slu4coder/The-Minimal-64-Home-Computer/Revision 1.2/KiCAD/8-Bit CPU 32k.kicad_sch

## KiCad design Revision 1.2/KiCAD/8-Bit CPU 32k.kicad_sch (2023-07-08)

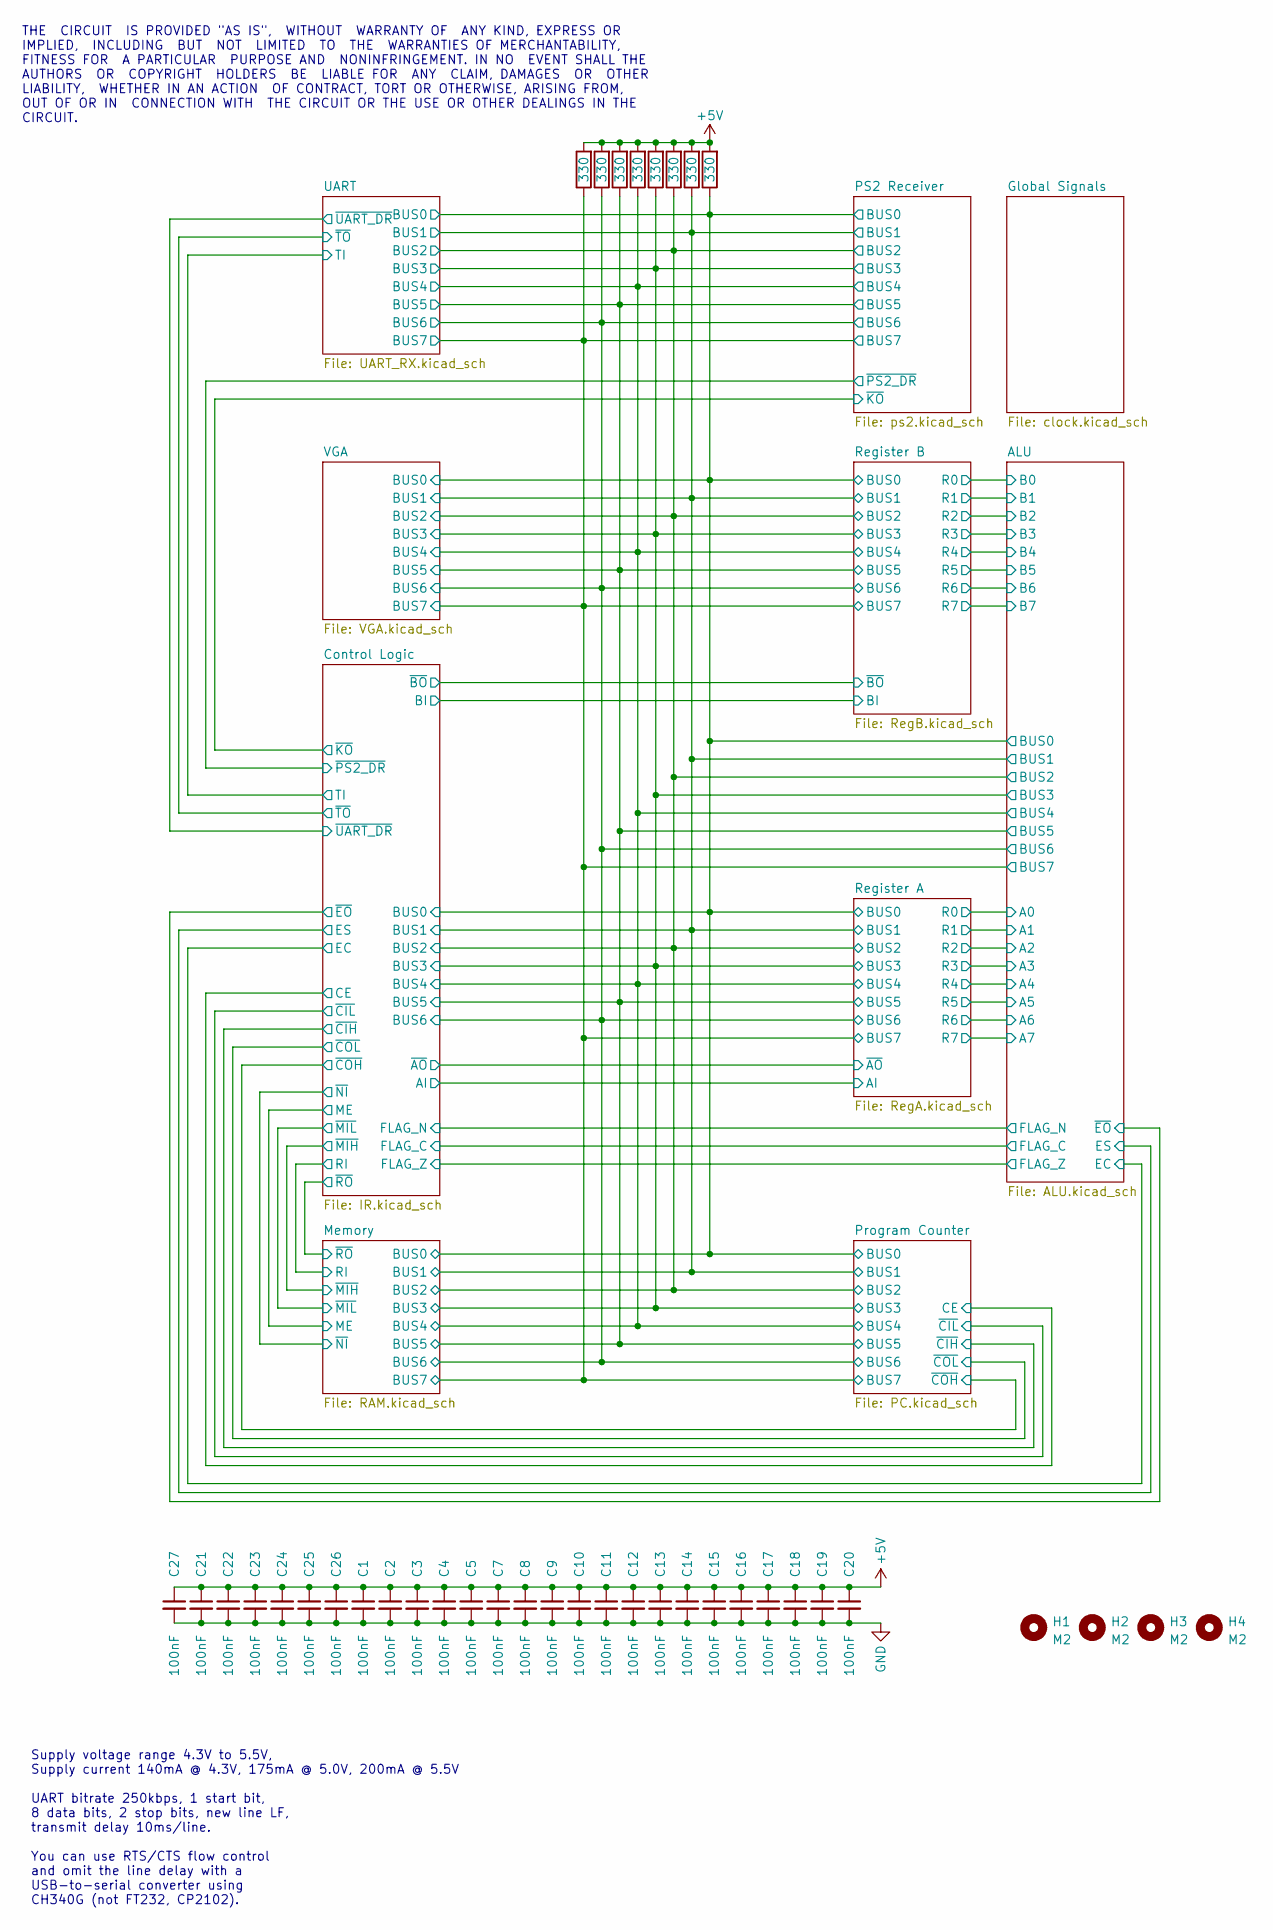
[picture p12: schematic 8-Bit CPU 32k.kicad_sch]

Parts:
C1, C2, C3, C4, C5, C7, C8, C9, C10, C11, C12, C13, C14, C15, C16, C17, C18, C19, C20, C21, C22, C23, C24, C25, C26, C27: 100nF; C_Disc_D3.4mm_W2.1mm_P2.50mm
H1, H2, H3, H4: M2; MountingHole_2.2mm_M2
R25, R26, R27, R28, R29, R30, R31, R32: 330; R_Axial_DIN0207_L6.3mm_D2.5mm_P7.62mm_Horizontal

Connections:
+5V: C1.1, C2.1, C3.1, C4.1, C5.1, C7.1, C8.1, C9.1, C10.1, C11.1, C12.1, C13.1, C14.1, C15.1, C16.1, C17.1, C18.1, C19.1, C20.1, C21.1, C22.1, C23.1, C24.1, C25.1, C26.1, C27.1, R25.2, R26.2, R27.2, R28.2, R29.2, R30.2, R31.2, R32.2
BUS0: R32.1
BUS1: R31.1
BUS2: R30.1
BUS3: R29.1
BUS4: R28.1
BUS5: R27.1
BUS6: R26.1
BUS7: R25.1
GND: C1.2, C2.2, C3.2, C4.2, C5.2, C7.2, C8.2, C9.2, C10.2, C11.2, C12.2, C13.2, C14.2, C15.2, C16.2, C17.2, C18.2, C19.2, C20.2, C21.2, C22.2, C23.2, C24.2, C25.2, C26.2, C27.2

Notes on the sheet:
Supply voltage range 4.3V to 5.5V, Supply current 140mA @ 4.3V, 175mA @ 5.0V, 200mA @ 5.5V UART bitrate 250kbps, 1 start bit, 8 data bits, 2 stop bits, new line LF, transmit delay 10ms/line. You can use RTS/CTS flow control and omit the line delay with a USB-to-serial converter using CH340G (not FT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
THE CIRCUIT IS PROVIDED "AS IS", WITHOUT WARRANTY OF ANY KIND, EXPRESS OR IMPLIED, INCLUDING BUT NOT LIMITED TO THE WARRANTIES OF MERCHANTABILITY, FITNESS FOR A PARTICULAR PURPOSE AND NONINFRINGEMENT. IN NO EVENT SHALL THE AUTHORS OR COPYRIGHT HOLDERS BE LIABLE FOR ANY CLAIM, DAMAGES OR OTHER LIABI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
