slu4coder/The-Minimal-64-Home-Computer/Revision 1.2/KiCAD/ALU.kicad_sch

## KiCad design Revision 1.2/KiCAD/ALU.kicad_sch (2023-07-08)

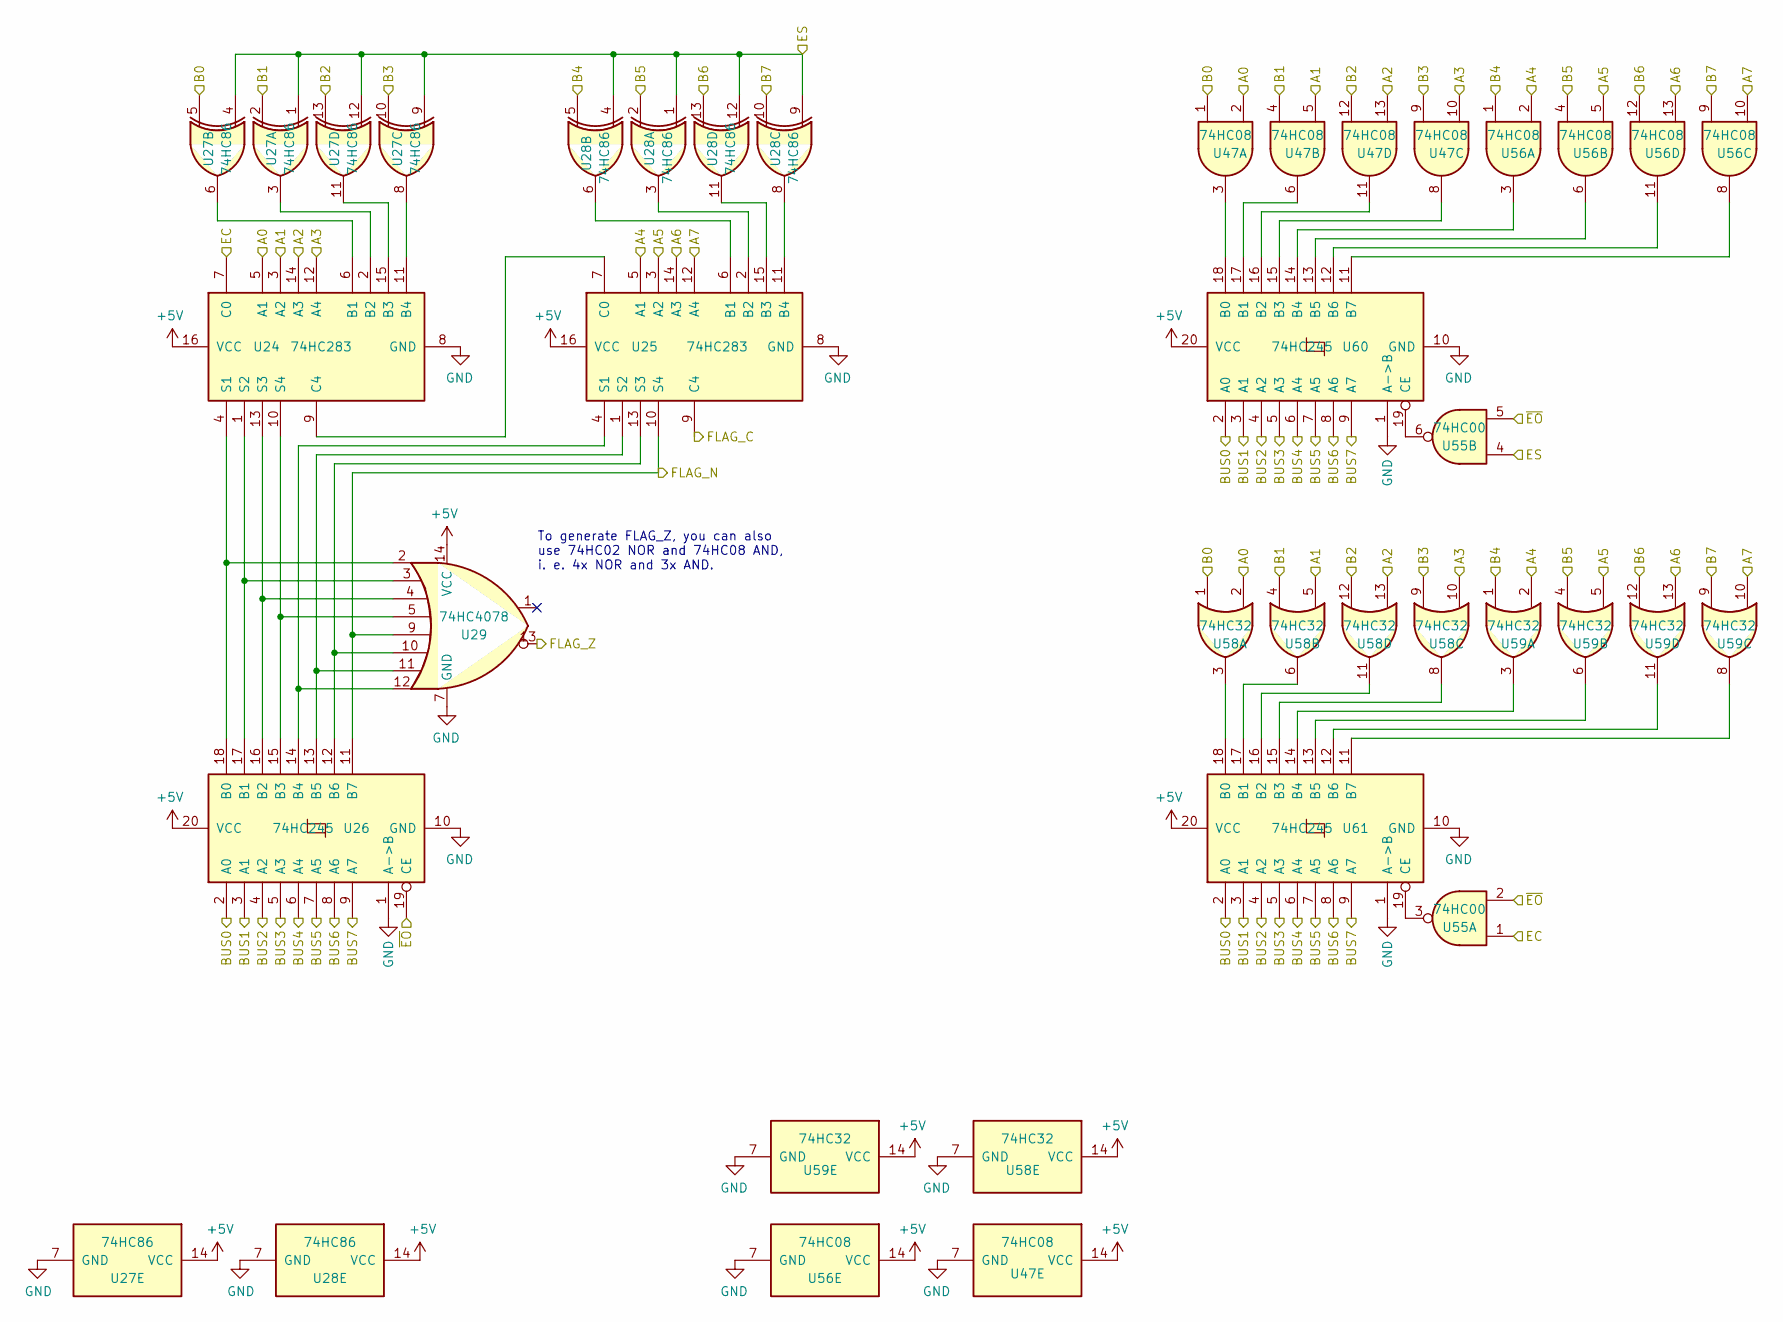
[picture p13: schematic ALU.kicad_sch]

Parts:
U24, U25: 74HC283; DIP-16_W7.62mm
U26, U60, U61: 74HC245; DIP-20_W7.62mm
U27, U28: 74HC86; DIP-14_W7.62mm
U29: 74HC4078; DIP-14_W7.62mm
U47, U56: 74HC08; DIP-14_W7.62mm
U55: 74HC00; DIP-14_W7.62mm
U58, U59: 74HC32; DIP-14_W7.62mm

Connections:
+5V: U24.16 (VCC), U25.16 (VCC), U26.20 (VCC), U27.14 (VCC), U28.14 (VCC), U29.14 (VCC), U47.14 (VCC), U56.14 (VCC), U58.14 (VCC), U59.14 (VCC), U60.20 (VCC), U61.20 (VCC)
A0: U24.5 (A1), U47.2, U58.2
A1: U24.3 (A2), U47.5, U58.5
A2: U24.14 (A3), U47.13, U58.13
A3: U24.12 (A4), U47.10, U58.10
A4: U25.5 (A1), U56.2, U59.2
A5: U25.3 (A2), U56.5, U59.5
A6: U25.14 (A3), U56.13, U59.13
A7: U25.12 (A4), U56.10, U59.10
B0: U27.5, U47.1, U58.1
B1: U27.2, U47.4, U58.4
B2: U27.13, U47.12, U58.12
B3: U27.10, U47.9, U58.9
B4: U28.5, U56.1, U59.1
B5: U28.2, U56.4, U59.4
B6: U28.13, U56.12, U59.12
B7: U28.10, U56.9, U59.9
BUS0: U26.2 (A0), U60.2 (A0), U61.2 (A0)
BUS1: U26.3 (A1), U60.3 (A1), U61.3 (A1)
BUS2: U26.4 (A2), U60.4 (A2), U61.4 (A2)
BUS3: U26.5 (A3), U60.5 (A3), U61.5 (A3)
BUS4: U26.6 (A4), U60.6 (A4), U61.6 (A4)
BUS5: U26.7 (A5), U60.7 (A5), U61.7 (A5)
BUS6: U26.8 (A6), U60.8 (A6), U61.8 (A6)
BUS7: U26.9 (A7), U60.9 (A7), U61.9 (A7)
EC: U24.7 (C0), U55.1
ES: U27.1, U27.4, U27.9, U27.12, U28.1, U28.4, U28.9, U28.12, U55.4
FLAG_C: U25.9 (C4)
FLAG_N: U25.10 (S4), U26.11 (B7), U29.9
FLAG_Z: U29.13
GND: U24.8 (GND), U25.8 (GND), U26.1 (A->B), U26.10 (GND), U27.7 (GND), U28.7 (GND), U29.7 (GND), U47.7 (GND), U56.7 (GND), U58.7 (GND), U59.7 (GND), U60.1 (A->B), U60.10 (GND), U61.1 (A->B), U61.10 (GND)
unnamed: U24.1 (S2), U26.17 (B1), U29.3
unnamed: U24.2 (B2), U27.3
unnamed: U24.4 (S1), U26.18 (B0), U29.2
unnamed: U24.6 (B1), U27.6
unnamed: U24.9 (C4), U25.7 (C0)
unnamed: U24.10 (S4), U26.15 (B3), U29.5
unnamed: U24.11 (B4), U27.8
unnamed: U24.13 (S3), U26.16 (B2), U29.4
unnamed: U24.15 (B3), U27.11
unnamed: U25.1 (S2), U26.13 (B5), U29.11
unnamed: U25.2 (B2), U28.3
unnamed: U25.4 (S1), U26.14 (B4), U29.12
unnamed: U25.6 (B1), U28.6
unnamed: U25.11 (B4), U28.8
unnamed: U25.13 (S3), U26.12 (B6), U29.10
unnamed: U25.15 (B3), U28.11
unnamed: U47.3, U60.18 (B0)
unnamed: U47.6, U60.17 (B1)
unnamed: U47.8, U60.15 (B3)
unnamed: U47.11, U60.16 (B2)
unnamed: U55.3, U61.19 (CE)
unnamed: U55.6, U60.19 (CE)
unnamed: U56.3, U60.14 (B4)
unnamed: U56.6, U60.13 (B5)
unnamed: U56.8, U60.11 (B7)
unnamed: U56.11, U60.12 (B6)
unnamed: U58.3, U61.18 (B0)
unnamed: U58.6, U61.17 (B1)
unnamed: U58.8, U61.15 (B3)
unnamed: U58.11, U61.16 (B2)
unnamed: U59.3, U61.14 (B4)
unnamed: U59.6, U61.13 (B5)
unnamed: U59.8, U61.11 (B7)
unnamed: U59.11, U61.12 (B6)
~EO: U26.19 (CE), U55.2, U55.5

Notes on the sheet:
To generate FLAG_Z, you can also use 74HC02 NOR and 74HC08 AND, i. e. 4x NOR and 3x AND.
