slu4coder/The-Minimal-64-Home-Computer/Revision 1.2/KiCAD/IR.kicad_sch

## KiCad design Revision 1.2/KiCAD/IR.kicad_sch (2023-07-08)

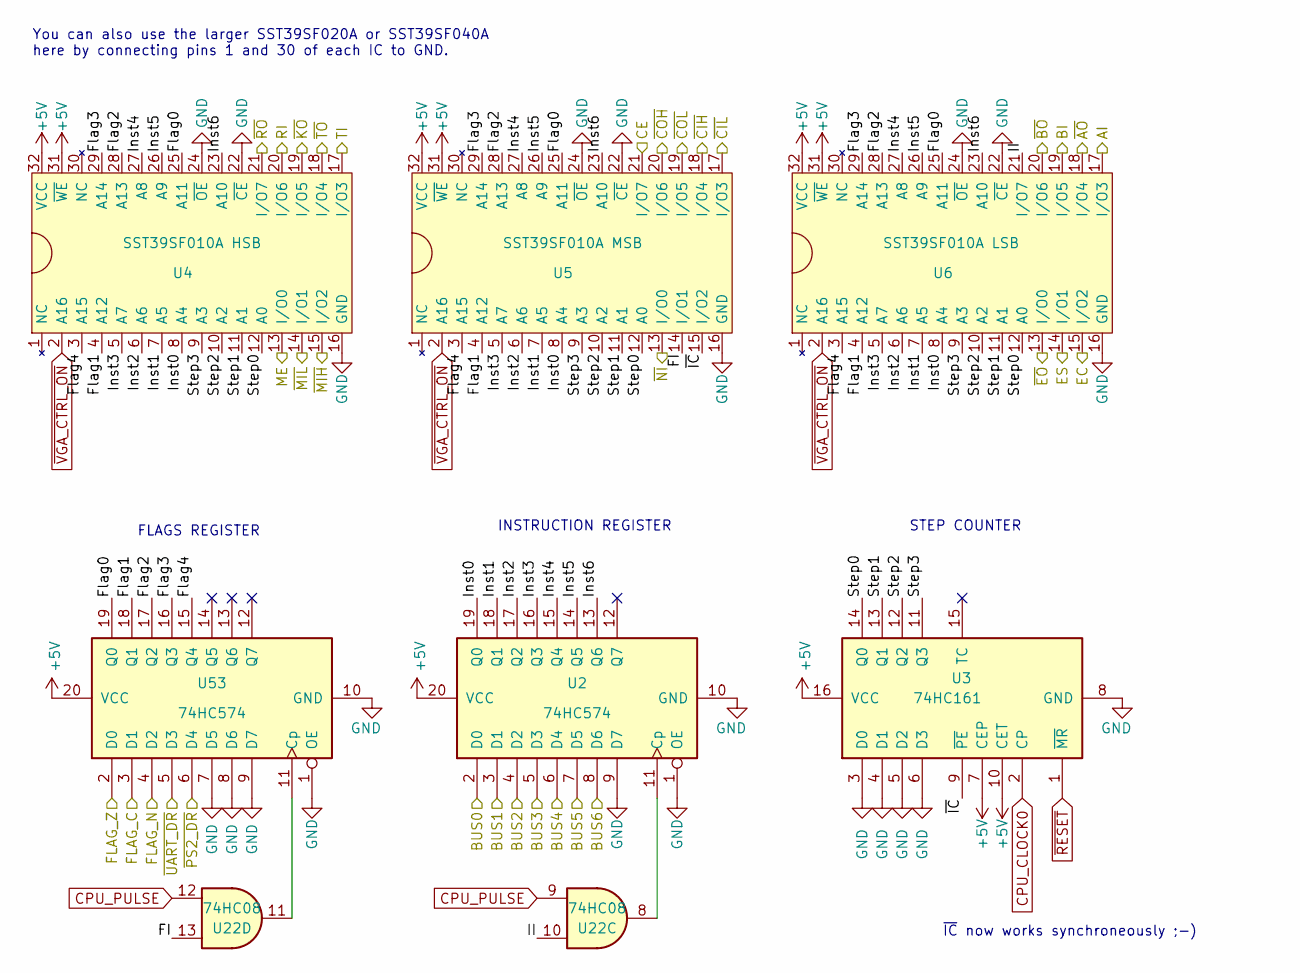
[picture p14: schematic IR.kicad_sch]

Parts:
U2, U53: 74HC574; DIP-20_W7.62mm
U3: 74HC161; DIP-16_W7.62mm
U4: SST39SF010A HSB; DIP-32_W15.24mm_Socket
U5: SST39SF010A MSB; DIP-32_W15.24mm_Socket
U6: SST39SF010A LSB; DIP-32_W15.24mm_Socket
U22: 74HC08; DIP-14_W7.62mm

Connections:
+5V: U2.20 (VCC), U3.7 (CEP), U3.10 (CET), U3.16 (VCC), U4.31 (~WE), U4.32 (VCC), U5.31 (~WE), U5.32 (VCC), U6.31 (~WE), U6.32 (VCC), U53.20 (VCC)
AI: U6.17 (I/O3)
BI: U6.19 (I/O5)
BUS0: U2.2 (D0)
BUS1: U2.3 (D1)
BUS2: U2.4 (D2)
BUS3: U2.5 (D3)
BUS4: U2.6 (D4)
BUS5: U2.7 (D5)
BUS6: U2.8 (D6)
CE: U5.21 (I/O7)
CPU_CLOCK0: U3.2 (CP)
CPU_PULSE: U22.9, U22.12
EC: U6.15 (I/O2)
ES: U6.14 (I/O1)
FI: U5.14 (I/O1), U22.13
FLAG_C: U53.3 (D1)
FLAG_N: U53.4 (D2)
FLAG_Z: U53.2 (D0)
Flag0: U4.25 (A11), U5.25 (A11), U6.25 (A11), U53.19 (Q0)
Flag1: U4.4 (A12), U5.4 (A12), U6.4 (A12), U53.18 (Q1)
Flag2: U4.28 (A13), U5.28 (A13), U6.28 (A13), U53.17 (Q2)
Flag3: U4.29 (A14), U5.29 (A14), U6.29 (A14), U53.16 (Q3)
Flag4: U4.3 (A15), U5.3 (A15), U6.3 (A15), U53.15 (Q4)
GND: U2.1 (OE), U2.9 (D7), U2.10 (GND), U3.3 (D0), U3.4 (D1), U3.5 (D2), U3.6 (D3), U3.8 (GND), U4.16 (GND), U4.22 (~CE), U4.24 (~OE), U5.16 (GND), U5.22 (~CE), U5.24 (~OE), U6.16 (GND), U6.22 (~CE), U6.24 (~OE), U53.1 (OE), U53.7 (D5), U53.8 (D6), U53.9 (D7), U53.10 (GND)
II: U6.21 (I/O7), U22.10
Inst0: U2.19 (Q0), U4.8 (A4), U5.8 (A4), U6.8 (A4)
Inst1: U2.18 (Q1), U4.7 (A5), U5.7 (A5), U6.7 (A5)
Inst2: U2.17 (Q2), U4.6 (A6), U5.6 (A6), U6.6 (A6)
Inst3: U2.16 (Q3), U4.5 (A7), U5.5 (A7), U6.5 (A7)
Inst4: U2.15 (Q4), U4.27 (A8), U5.27 (A8), U6.27 (A8)
Inst5: U2.14 (Q5), U4.26 (A9), U5.26 (A9), U6.26 (A9)
Inst6: U2.13 (Q6), U4.23 (A10), U5.23 (A10), U6.23 (A10)
ME: U4.13 (I/O0)
unnamed: U2.11 (Cp), U22.8
unnamed: U22.11, U53.11 (Cp)
RI: U4.20 (I/O6)
Step0: U3.14 (Q0), U4.12 (A0), U5.12 (A0), U6.12 (A0)
Step1: U3.13 (Q1), U4.11 (A1), U5.11 (A1), U6.11 (A1)
Step2: U3.12 (Q2), U4.10 (A2), U5.10 (A2), U6.10 (A2)
Step3: U3.11 (Q3), U4.9 (A3), U5.9 (A3), U6.9 (A3)
TI: U4.17 (I/O3)
~AO: U6.18 (I/O4)
~BO: U6.20 (I/O6)
~CIH: U5.18 (I/O4)
~CIL: U5.17 (I/O3)
~COH: U5.20 (I/O6)
~COL: U5.19 (I/O5)
~EO: U6.13 (I/O0)
~IC: U3.9 (~PE), U5.15 (I/O2)
~KO: U4.19 (I/O5)
~MIH: U4.15 (I/O2)
~MIL: U4.14 (I/O1)
~NI: U5.13 (I/O0)
~PS2_DR: U53.6 (D4)
~RESET: U3.1 (~MR)
~RO: U4.21 (I/O7)
~TO: U4.18 (I/O4)
~UART_DR: U53.5 (D3)
~VGA_CTRL_ON: U4.2 (A16), U5.2 (A16), U6.2 (A16)

Notes on the sheet:
FLAGS REGISTER
~{IC} now works synchroneously ;-)
INSTRUCTION REGISTER
You can also use the larger SST39SF020A or SST39SF040A here by connecting pins 1 and 30 of each IC to GND.
STEP COUNTER
