slu4coder/The-Minimal-64-Home-Computer/Revision 1.2/KiCAD/PC.kicad_sch

## KiCad design Revision 1.2/KiCAD/PC.kicad_sch (2023-07-08)

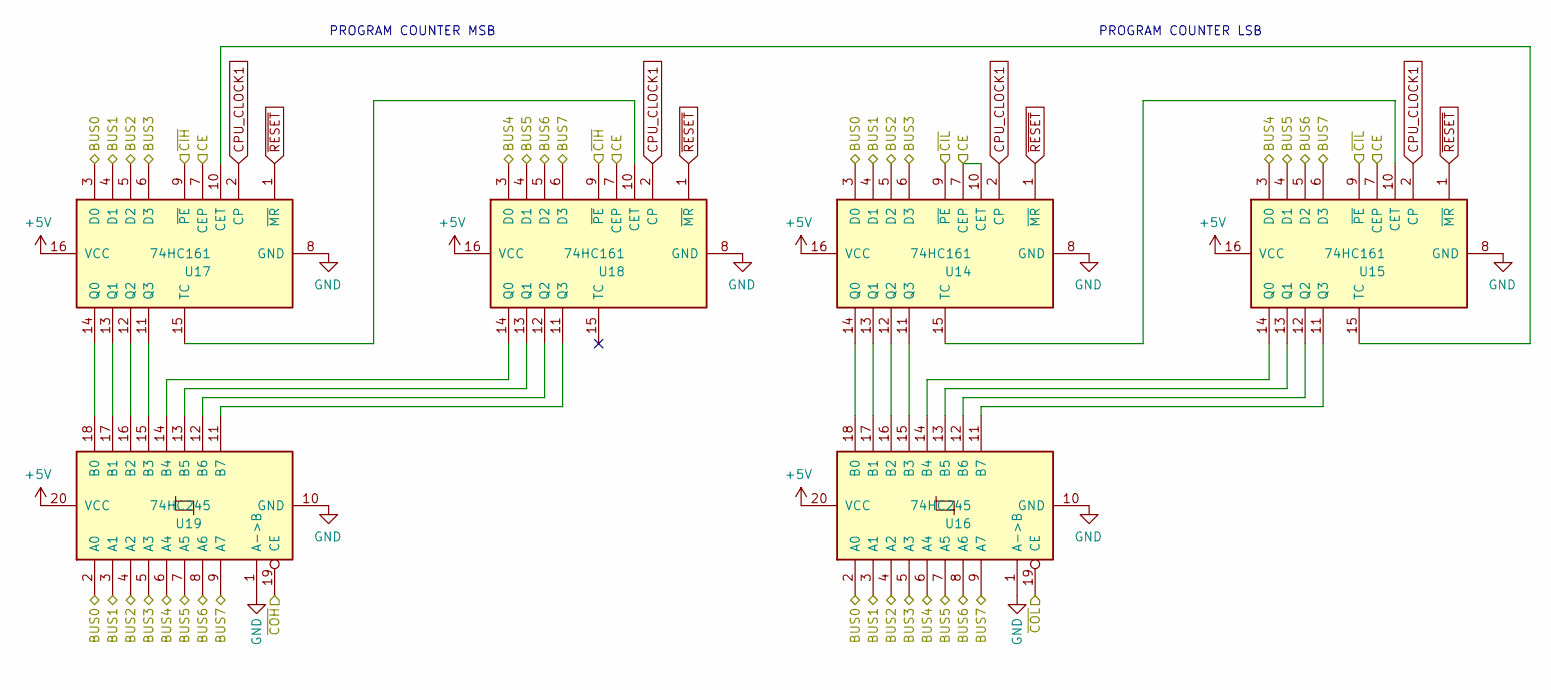
[picture p15: schematic PC.kicad_sch]

Parts:
U14, U15, U17, U18: 74HC161; DIP-16_W7.62mm
U16, U19: 74HC245; DIP-20_W7.62mm

Connections:
+5V: U14.16 (VCC), U15.16 (VCC), U16.20 (VCC), U17.16 (VCC), U18.16 (VCC), U19.20 (VCC)
BUS0: U14.3 (D0), U16.2 (A0), U17.3 (D0), U19.2 (A0)
BUS1: U14.4 (D1), U16.3 (A1), U17.4 (D1), U19.3 (A1)
BUS2: U14.5 (D2), U16.4 (A2), U17.5 (D2), U19.4 (A2)
BUS3: U14.6 (D3), U16.5 (A3), U17.6 (D3), U19.5 (A3)
BUS4: U15.3 (D0), U16.6 (A4), U18.3 (D0), U19.6 (A4)
BUS5: U15.4 (D1), U16.7 (A5), U18.4 (D1), U19.7 (A5)
BUS6: U15.5 (D2), U16.8 (A6), U18.5 (D2), U19.8 (A6)
BUS7: U15.6 (D3), U16.9 (A7), U18.6 (D3), U19.9 (A7)
CE: U14.7 (CEP), U14.10 (CET), U15.7 (CEP), U17.7 (CEP), U18.7 (CEP)
CPU_CLOCK1: U14.2 (CP), U15.2 (CP), U17.2 (CP), U18.2 (CP)
GND: U14.8 (GND), U15.8 (GND), U16.1 (A->B), U16.10 (GND), U17.8 (GND), U18.8 (GND), U19.1 (A->B), U19.10 (GND)
unnamed: U14.11 (Q3), U16.15 (B3)
unnamed: U14.12 (Q2), U16.16 (B2)
unnamed: U14.13 (Q1), U16.17 (B1)
unnamed: U14.14 (Q0), U16.18 (B0)
unnamed: U14.15 (TC), U15.10 (CET)
unnamed: U15.11 (Q3), U16.11 (B7)
unnamed: U15.12 (Q2), U16.12 (B6)
unnamed: U15.13 (Q1), U16.13 (B5)
unnamed: U15.14 (Q0), U16.14 (B4)
unnamed: U15.15 (TC), U17.10 (CET)
unnamed: U17.11 (Q3), U19.15 (B3)
unnamed: U17.12 (Q2), U19.16 (B2)
unnamed: U17.13 (Q1), U19.17 (B1)
unnamed: U17.14 (Q0), U19.18 (B0)
unnamed: U17.15 (TC), U18.10 (CET)
unnamed: U18.11 (Q3), U19.11 (B7)
unnamed: U18.12 (Q2), U19.12 (B6)
unnamed: U18.13 (Q1), U19.13 (B5)
unnamed: U18.14 (Q0), U19.14 (B4)
~CIH: U17.9 (~PE), U18.9 (~PE)
~CIL: U14.9 (~PE), U15.9 (~PE)
~COH: U19.19 (CE)
~COL: U16.19 (CE)
~RESET: U14.1 (~MR), U15.1 (~MR), U17.1 (~MR), U18.1 (~MR)

Notes on the sheet:
PROGRAM COUNTER MSB
PROGRAM COUNTER LSB
