slu4coder/The-Minimal-64-Home-Computer/Revision 1.2/KiCAD/RAM.kicad_sch

## KiCad design Revision 1.2/KiCAD/RAM.kicad_sch (2023-07-08)

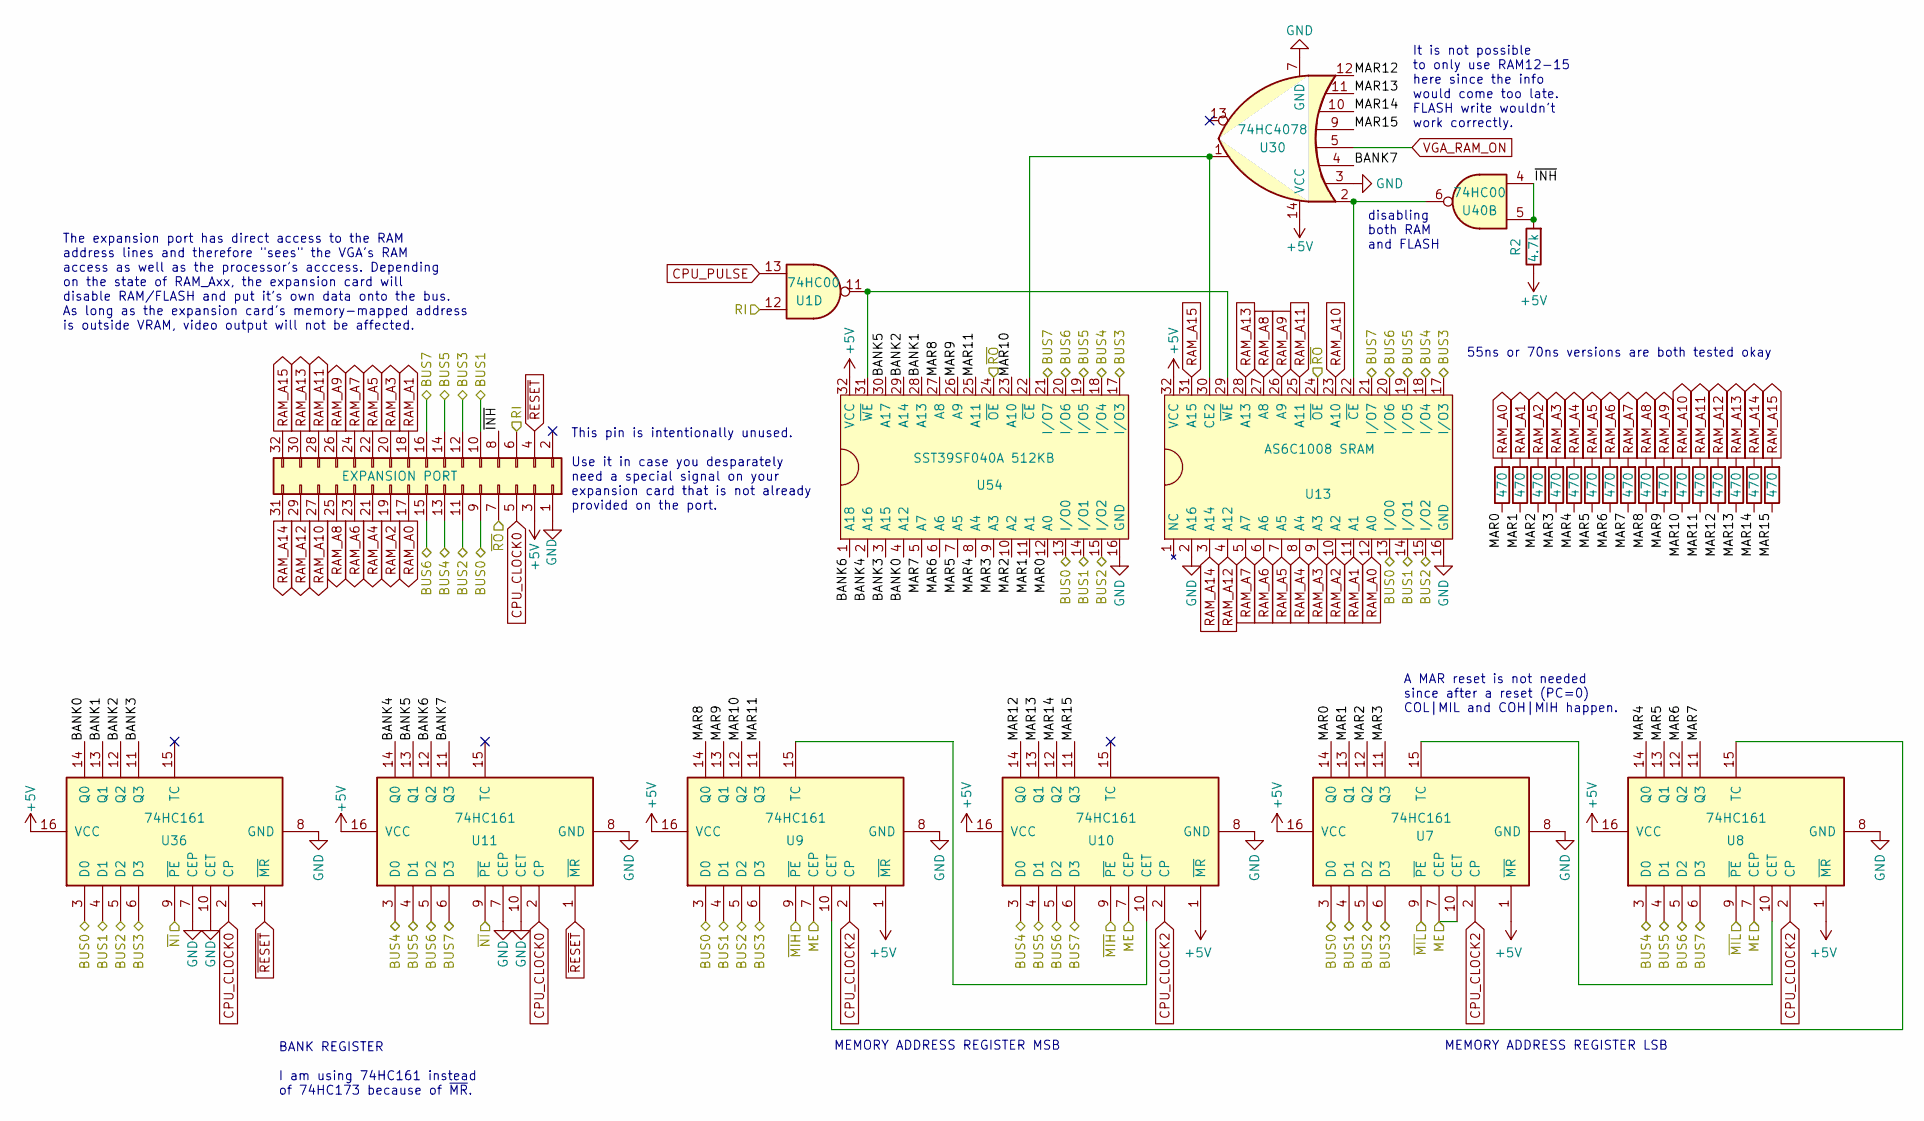
[picture p16: schematic RAM.kicad_sch]

Parts:
J3: EXPANSION PORT; PinSocket_2x16_P2.54mm_Vertical
R2: 4.7k; R_Axial_DIN0207_L6.3mm_D2.5mm_P7.62mm_Horizontal
R5, R6, R7, R8, R9, R10, R11, R12, R13, R14, R15, R16, R17, R18, R19, R20: 470; R_Axial_DIN0207_L6.3mm_D2.5mm_P7.62mm_Horizontal
U1, U40: 74HC00; DIP-14_W7.62mm
U7, U8, U9, U10, U11, U36: 74HC161; DIP-16_W7.62mm
U13: AS6C1008 SRAM; DIP-32_W15.24mm
U30: 74HC4078; DIP-14_W7.62mm
U54: SST39SF040A 512KB; DIP-32_W15.24mm_Socket

Connections:
+5V: J3.3, R2.1, U7.1 (~MR), U7.16 (VCC), U8.1 (~MR), U8.16 (VCC), U9.1 (~MR), U9.16 (VCC), U10.1 (~MR), U10.16 (VCC), U11.16 (VCC), U13.32 (VCC), U30.14 (VCC), U36.16 (VCC), U54.32 (VCC)
BANK0: U36.14 (Q0), U54.4 (A12)
BANK1: U36.13 (Q1), U54.28 (A13)
BANK2: U36.12 (Q2), U54.29 (A14)
BANK3: U36.11 (Q3), U54.3 (A15)
BANK4: U11.14 (Q0), U54.2 (A16)
BANK5: U11.13 (Q1), U54.30 (A17)
BANK6: U11.12 (Q2), U54.1 (A18)
BANK7: U11.11 (Q3), U30.4
BUS0: J3.9, U7.3 (D0), U9.3 (D0), U13.13 (I/O0), U36.3 (D0), U54.13 (I/O0)
BUS1: J3.10, U7.4 (D1), U9.4 (D1), U13.14 (I/O1), U36.4 (D1), U54.14 (I/O1)
BUS2: J3.11, U7.5 (D2), U9.5 (D2), U13.15 (I/O2), U36.5 (D2), U54.15 (I/O2)
BUS3: J3.12, U7.6 (D3), U9.6 (D3), U13.17 (I/O3), U36.6 (D3), U54.17 (I/O3)
BUS4: J3.13, U8.3 (D0), U10.3 (D0), U11.3 (D0), U13.18 (I/O4), U54.18 (I/O4)
BUS5: J3.14, U8.4 (D1), U10.4 (D1), U11.4 (D1), U13.19 (I/O5), U54.19 (I/O5)
BUS6: J3.15, U8.5 (D2), U10.5 (D2), U11.5 (D2), U13.20 (I/O6), U54.20 (I/O6)
BUS7: J3.16, U8.6 (D3), U10.6 (D3), U11.6 (D3), U13.21 (I/O7), U54.21 (I/O7)
CPU_CLOCK0: J3.5, U11.2 (CP), U36.2 (CP)
CPU_CLOCK2: U7.2 (CP), U8.2 (CP), U9.2 (CP), U10.2 (CP)
CPU_PULSE: U1.13
GND: J3.1, U7.8 (GND), U8.8 (GND), U9.8 (GND), U10.8 (GND), U11.7 (CEP), U11.8 (GND), U11.10 (CET), U13.2 (A16), U13.16 (GND), U30.3, U30.7 (GND), U36.7 (CEP), U36.8 (GND), U36.10 (CET), U54.16 (GND)
MAR0: R17.1, U7.14 (Q0), U54.12 (A0)
MAR1: R18.1, U7.13 (Q1), U54.11 (A1)
MAR2: R19.1, U7.12 (Q2), U54.10 (A2)
MAR3: R20.1, U7.11 (Q3), U54.9 (A3)
MAR4: R13.1, U8.14 (Q0), U54.8 (A4)
MAR5: R14.1, U8.13 (Q1), U54.7 (A5)
MAR6: R15.1, U8.12 (Q2), U54.6 (A6)
MAR7: R16.1, U8.11 (Q3), U54.5 (A7)
MAR8: R5.1, U9.14 (Q0), U54.27 (A8)
MAR9: R6.1, U9.13 (Q1), U54.26 (A9)
MAR10: R7.1, U9.12 (Q2), U54.23 (A10)
MAR11: R8.1, U9.11 (Q3), U54.25 (A11)
MAR12: R9.1, U10.14 (Q0), U30.12
MAR13: R10.1, U10.13 (Q1), U30.11
MAR14: R11.1, U10.12 (Q2), U30.10
MAR15: R12.1, U10.11 (Q3), U30.9
ME: U7.7 (CEP), U7.10 (CET), U8.7 (CEP), U9.7 (CEP), U10.7 (CEP)
unnamed: U1.11, U13.29 (~WE), U54.31 (~WE)
unnamed: U7.15 (TC), U8.10 (CET)
unnamed: U8.15 (TC), U9.10 (CET)
unnamed: U9.15 (TC), U10.10 (CET)
unnamed: U13.22 (~CE), U30.2, U40.6
unnamed: U13.30 (CE2), U30.1, U54.22 (~CE)
RAM_A0: J3.17, R17.2, U13.12 (A0)
RAM_A1: J3.18, R18.2, U13.11 (A1)
RAM_A2: J3.19, R19.2, U13.10 (A2)
RAM_A3: J3.20, R20.2, U13.9 (A3)
RAM_A4: J3.21, R13.2, U13.8 (A4)
RAM_A5: J3.22, R14.2, U13.7 (A5)
RAM_A6: J3.23, R15.2, U13.6 (A6)
RAM_A7: J3.24, R16.2, U13.5 (A7)
RAM_A8: J3.25, R5.2, U13.27 (A8)
RAM_A9: J3.26, R6.2, U13.26 (A9)
RAM_A10: J3.27, R7.2, U13.23 (A10)
RAM_A11: J3.28, R8.2, U13.25 (A11)
RAM_A12: J3.29, R9.2, U13.4 (A12)
RAM_A13: J3.30, R10.2, U13.28 (A13)
RAM_A14: J3.31, R11.2, U13.3 (A14)
RAM_A15: J3.32, R12.2, U13.31 (A15)
RI: J3.6, U1.12
VGA_RAM_ON: U30.5
~INH: J3.8, R2.2, U40.4, U40.5
~MIH: U9.9 (~PE), U10.9 (~PE)
~MIL: U7.9 (~PE), U8.9 (~PE)
~NI: U11.9 (~PE), U36.9 (~PE)
~RESET: J3.4, U11.1 (~MR), U36.1 (~MR)
~RO: J3.7, U13.24 (~OE), U54.24 (~OE)

Notes on the sheet:
55ns or 70ns versions are both tested okay
disabling both RAM and FLASH
MEMORY ADDRESS REGISTER MSB
It is not possible to only use RAM12-15 here since the info would come too late. FLASH write wouldn't work correctly.
A MAR reset is not needed since after a reset (PC=0) COL|MIL and COH|MIH happen.
MEMORY ADDRESS REGISTER LSB
This pin is intentionally unused. Use it in case you desparately need a special signal on your expansion card that is not already provided on the port.
BANK REGISTER I am using 74HC161 instead of 74HC173 because of ~{MR}.
The expansion port has direct access to the RAM address lines and therefore "sees" the VGA's RAM access as well as the processor's acccess. Depending on the state of RAM_Axx, the expansion card will disable RAM/FLASH and put it's own data onto the bus. As long as the expansion card's memory-mapped 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
