slu4coder/The-Minimal-64-Home-Computer/Revision 1.2/KiCAD/RegA.kicad_sch

## KiCad design Revision 1.2/KiCAD/RegA.kicad_sch (2023-07-08)

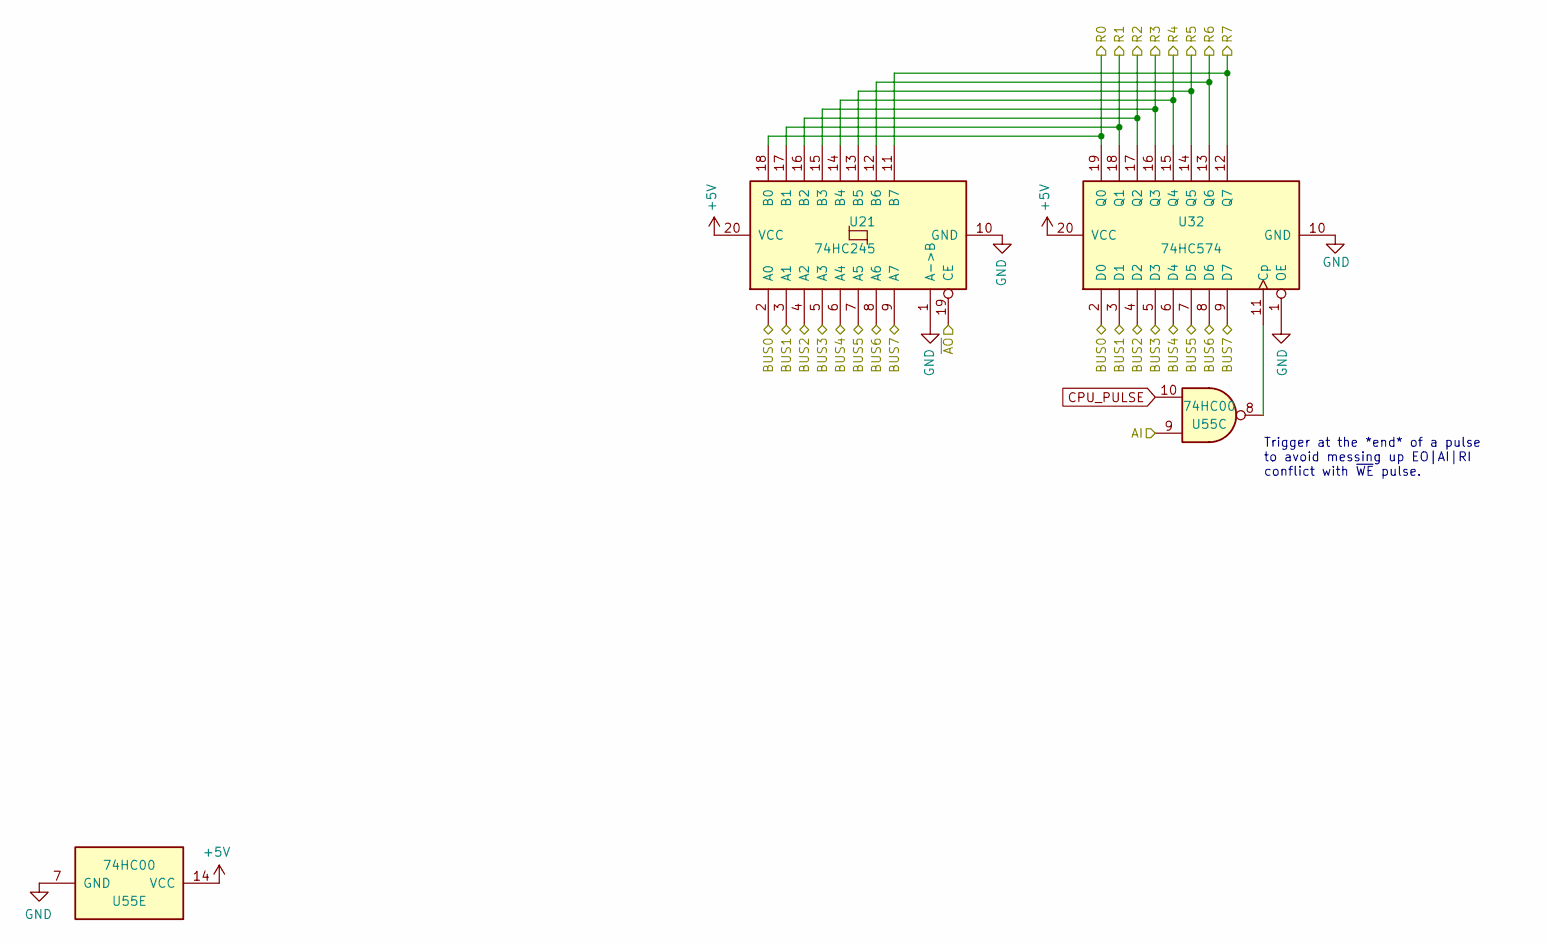
[picture p17: schematic RegA.kicad_sch]

Parts:
U21: 74HC245; DIP-20_W7.62mm
U32: 74HC574; DIP-20_W7.62mm
U55: 74HC00; DIP-14_W7.62mm

Connections:
+5V: U21.20 (VCC), U32.20 (VCC), U55.14 (VCC)
AI: U55.9
BUS0: U21.2 (A0), U32.2 (D0)
BUS1: U21.3 (A1), U32.3 (D1)
BUS2: U21.4 (A2), U32.4 (D2)
BUS3: U21.5 (A3), U32.5 (D3)
BUS4: U21.6 (A4), U32.6 (D4)
BUS5: U21.7 (A5), U32.7 (D5)
BUS6: U21.8 (A6), U32.8 (D6)
BUS7: U21.9 (A7), U32.9 (D7)
CPU_PULSE: U55.10
GND: U21.1 (A->B), U21.10 (GND), U32.1 (OE), U32.10 (GND), U55.7 (GND)
unnamed: U32.11 (Cp), U55.8
R0: U21.18 (B0), U32.19 (Q0)
R1: U21.17 (B1), U32.18 (Q1)
R2: U21.16 (B2), U32.17 (Q2)
R3: U21.15 (B3), U32.16 (Q3)
R4: U21.14 (B4), U32.15 (Q4)
R5: U21.13 (B5), U32.14 (Q5)
R6: U21.12 (B6), U32.13 (Q6)
R7: U21.11 (B7), U32.12 (Q7)
~AO: U21.19 (CE)

Notes on the sheet:
Trigger at the *end* of a pulse to avoid messing up EO|AI|RI conflict with ~{WE} pulse.
