slu4coder/The-Minimal-64-Home-Computer/Revision 1.2/KiCAD/RegB.kicad_sch

## KiCad design Revision 1.2/KiCAD/RegB.kicad_sch (2023-07-08)

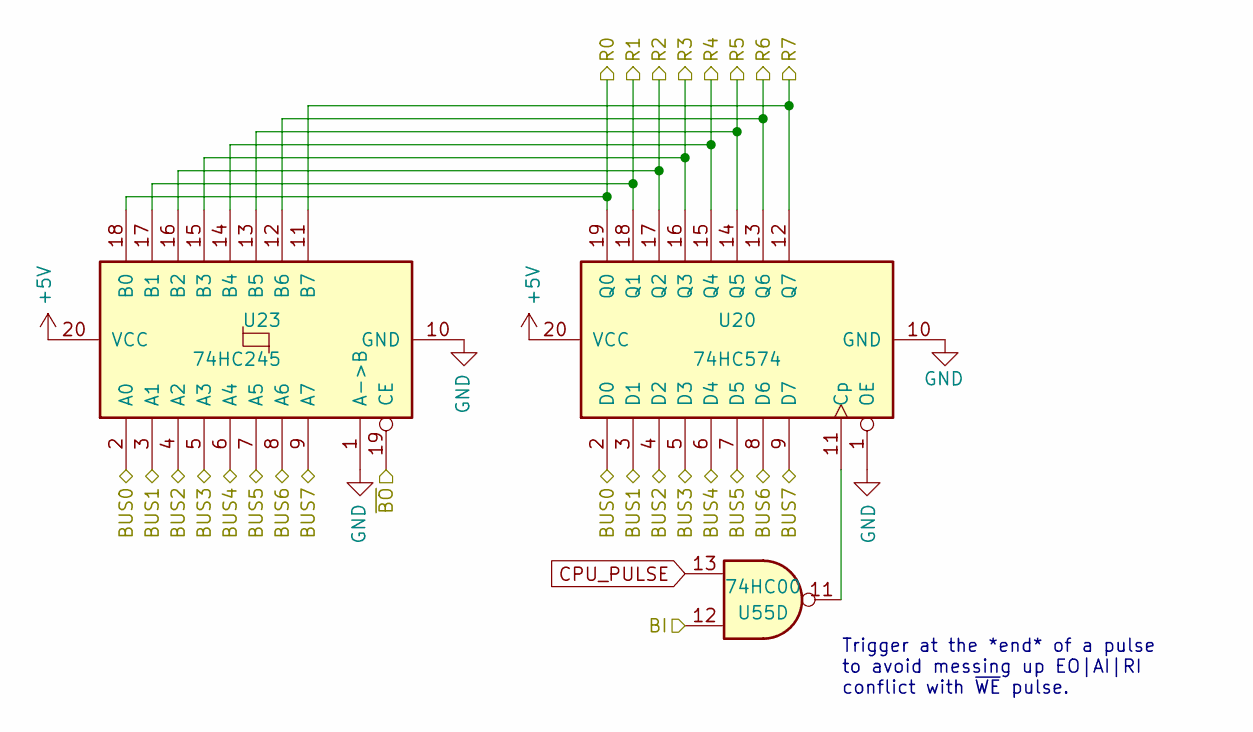
[picture p18: schematic RegB.kicad_sch]

Parts:
U20: 74HC574; DIP-20_W7.62mm
U23: 74HC245; DIP-20_W7.62mm
U55: 74HC00; DIP-14_W7.62mm

Connections:
+5V: U20.20 (VCC), U23.20 (VCC)
BI: U55.12
BUS0: U20.2 (D0), U23.2 (A0)
BUS1: U20.3 (D1), U23.3 (A1)
BUS2: U20.4 (D2), U23.4 (A2)
BUS3: U20.5 (D3), U23.5 (A3)
BUS4: U20.6 (D4), U23.6 (A4)
BUS5: U20.7 (D5), U23.7 (A5)
BUS6: U20.8 (D6), U23.8 (A6)
BUS7: U20.9 (D7), U23.9 (A7)
CPU_PULSE: U55.13
GND: U20.1 (OE), U20.10 (GND), U23.1 (A->B), U23.10 (GND)
unnamed: U20.11 (Cp), U55.11
R0: U20.19 (Q0), U23.18 (B0)
R1: U20.18 (Q1), U23.17 (B1)
R2: U20.17 (Q2), U23.16 (B2)
R3: U20.16 (Q3), U23.15 (B3)
R4: U20.15 (Q4), U23.14 (B4)
R5: U20.14 (Q5), U23.13 (B5)
R6: U20.13 (Q6), U23.12 (B6)
R7: U20.12 (Q7), U23.11 (B7)
~BO: U23.19 (CE)

Notes on the sheet:
Trigger at the *end* of a pulse to avoid messing up EO|AI|RI conflict with ~{WE} pulse.
