slu4coder/The-Minimal-64-Home-Computer/Revision 1.2/KiCAD/UART_RX.kicad_sch

## KiCad design Revision 1.2/KiCAD/UART_RX.kicad_sch (2023-07-08)

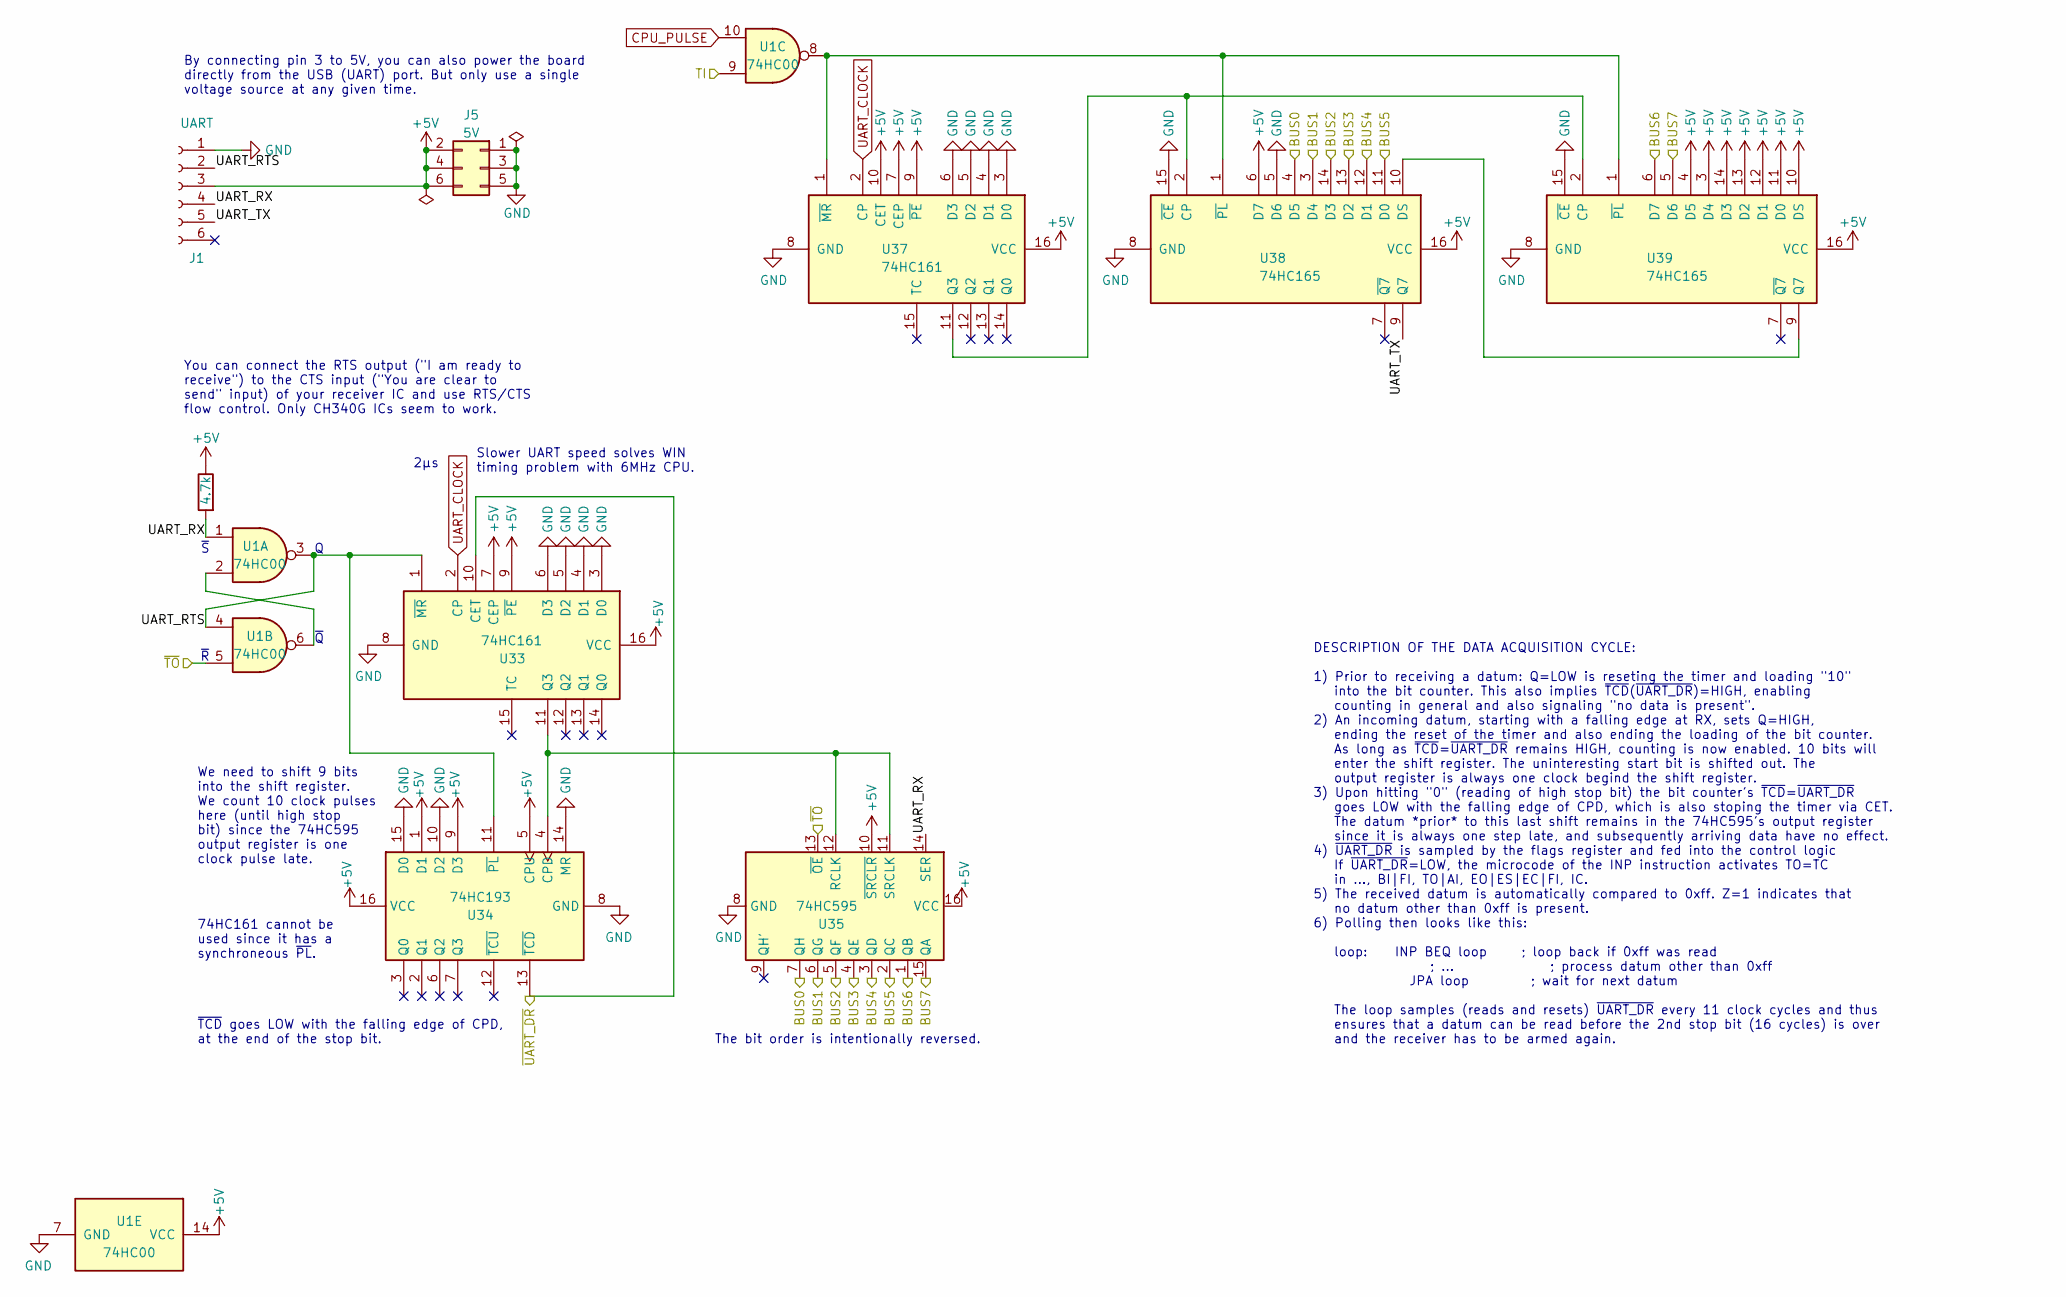
[picture p19: schematic UART_RX.kicad_sch]

Parts:
J1: UART; PinSocket_1x06_P2.54mm_Vertical
J5: 5V; PinSocket_2x03_P2.54mm_Vertical
R22: 4.7k; R_Axial_DIN0207_L6.3mm_D2.5mm_P7.62mm_Horizontal
U1: 74HC00; DIP-14_W7.62mm
U33, U37: 74HC161; DIP-16_W7.62mm
U34: 74HC193; DIP-16_W7.62mm
U35: 74HC595; DIP-16_W7.62mm
U38, U39: 74HC165; DIP-16_W7.62mm

Connections:
+5V: J1.3, J5.2, J5.4, J5.6, R22.1, U1.14 (VCC), U33.7 (CEP), U33.9 (~PE), U33.16 (VCC), U34.1 (D1), U34.5 (CPU), U34.9 (D3), U34.16 (VCC), U35.10 (~SRCLR), U35.16 (VCC), U37.7 (CEP), U37.9 (~PE), U37.10 (CET), U37.16 (VCC), U38.6 (D7), U38.16 (VCC), U39.3 (D4), U39.4 (D5), U39.10 (DS), U39.11 (D0), U39.12 (D1), U39.13 (D2), U39.14 (D3), U39.16 (VCC)
BUS0: U35.7 (QH), U38.4 (D5)
BUS1: U35.6 (QG), U38.3 (D4)
BUS2: U35.5 (QF), U38.14 (D3)
BUS3: U35.4 (QE), U38.13 (D2)
BUS4: U35.3 (QD), U38.12 (D1)
BUS5: U35.2 (QC), U38.11 (D0)
BUS6: U35.1 (QB), U39.6 (D7)
BUS7: U35.15 (QA), U39.5 (D6)
CPU_PULSE: U1.10
GND: J1.1, J5.1, J5.3, J5.5, U1.7 (GND), U33.3 (D0), U33.4 (D1), U33.5 (D2), U33.6 (D3), U33.8 (GND), U34.8 (GND), U34.10 (D2), U34.14 (MR), U34.15 (D0), U35.8 (GND), U37.3 (D0), U37.4 (D1), U37.5 (D2), U37.6 (D3), U37.8 (GND), U38.5 (D6), U38.8 (GND), U38.15 (~CE), U39.8 (GND), U39.15 (~CE)
unnamed: U1.2, U1.6
unnamed: U1.8, U37.1 (~MR), U38.1 (~PL), U39.1 (~PL)
unnamed: U33.11 (Q3), U34.4 (CPD), U35.11 (SRCLK), U35.12 (RCLK)
unnamed: U37.11 (Q3), U38.2 (CP), U39.2 (CP)
unnamed: U38.10 (DS), U39.9 (Q7)
TI: U1.9
UART_CLOCK: U33.2 (CP), U37.2 (CP)
UART_RTS: J1.2, U1.3, U1.4, U33.1 (~MR), U34.11 (~PL)
UART_RX: J1.4, R22.2, U1.1, U35.14 (SER)
UART_TX: J1.5, U38.9 (Q7)
~TO: U1.5, U35.13 (~OE)
~UART_DR: U33.10 (CET), U34.13 (~TCD)

Notes on the sheet:
Slower UART speed solves WIN timing problem with 6MHz CPU.
~{TCD} goes LOW with the falling edge of CPD, at the end of the stop bit.
74HC161 cannot be used since it has a synchroneous ~{PL}.
You can connect the RTS output ("I am ready to receive") to the CTS input ("You are clear to send" input) of your receiver IC and use RTS/CTS flow control. Only CH340G ICs seem to work.
We need to shift 9 bits into the shift register. We count 10 clock pulses here (until high stop bit) since the 74HC595 output register is one clock pulse late.
~{Q}
2µs
DESCRIPTION OF THE DATA ACQUISITION CYCLE: 1) Prior to receiving a datum: Q=LOW is reseting the timer and loading "10" into the bit counter. This also implies ~{TCD}(~{UART_DR})=HIGH, enabling counting in general and also signaling "no data is present". 2) An incoming datum, starting with a falling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
The bit order is intentionally reversed.
By connecting pin 3 to 5V, you can also power the board directly from the USB (UART) port. But only use a single voltage source at any given time.
~{S}
~{R}
