slu4coder/The-Minimal-64-Home-Computer/Revision 1.2/KiCAD/VGA.kicad_sch

## KiCad design Revision 1.2/KiCAD/VGA.kicad_sch (2023-07-08)

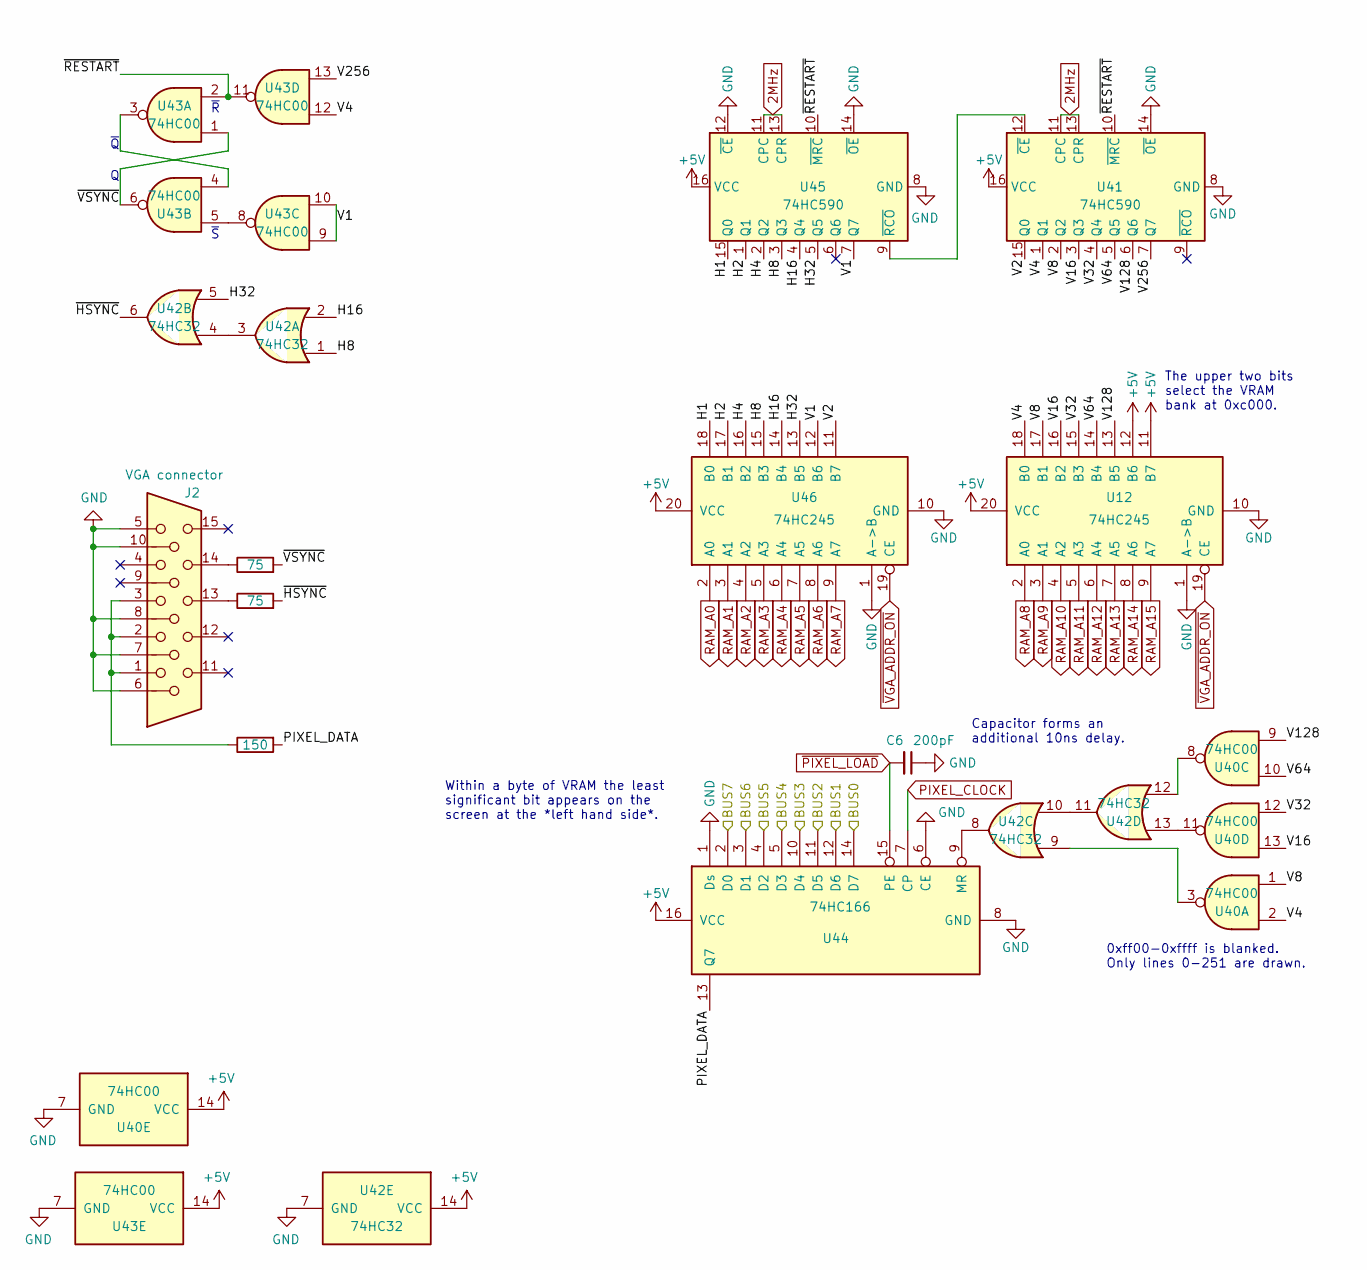
[picture p20: schematic VGA.kicad_sch]

Parts:
C6: 200pF; C_Disc_D3.4mm_W2.1mm_P2.50mm
J2: VGA connector; VGA DSUB15HD_female
R1, R3: 75; R_Axial_DIN0207_L6.3mm_D2.5mm_P7.62mm_Horizontal
R4: 150; R_Axial_DIN0207_L6.3mm_D2.5mm_P7.62mm_Horizontal
U12, U46: 74HC245; DIP-20_W7.62mm
U40, U43: 74HC00; DIP-14_W7.62mm
U41, U45: 74HC590; DIP-16_W7.62mm
U42: 74HC32; DIP-14_W7.62mm
U44: 74HC166; DIP-16_W7.62mm

Connections:
2MHz: U41.11 (CPC), U41.13 (CPR), U45.11 (CPC), U45.13 (CPR)
+5V: U12.11 (B7), U12.12 (B6), U12.20 (VCC), U40.14 (VCC), U41.16 (VCC), U42.14 (VCC), U43.14 (VCC), U44.16 (VCC), U45.16 (VCC), U46.20 (VCC)
BUS0: U44.14 (D7)
BUS1: U44.12 (D6)
BUS2: U44.11 (D5)
BUS3: U44.10 (D4)
BUS4: U44.5 (D3)
BUS5: U44.4 (D2)
BUS6: U44.3 (D1)
BUS7: U44.2 (D0)
GND: C6.1, J2.5, J2.6, J2.7, J2.8, J2.10, U12.1 (A->B), U12.10 (GND), U40.7 (GND), U41.8 (GND), U41.14 (~OE), U42.7 (GND), U43.7 (GND), U44.1 (Ds), U44.6 (CE), U44.8 (GND), U45.8 (GND), U45.12 (~CE), U45.14 (~OE), U46.1 (A->B), U46.10 (GND)
H1: U45.15 (Q0), U46.18 (B0)
H2: U45.1 (Q1), U46.17 (B1)
H4: U45.2 (Q2), U46.16 (B2)
H8: U42.1, U45.3 (Q3), U46.15 (B3)
H16: U42.2, U45.4 (Q4), U46.14 (B4)
H32: U42.5, U45.5 (Q5), U46.13 (B5)
unnamed: J2.1, J2.2, J2.3, R4.1
unnamed: J2.13, R3.1
unnamed: J2.14, R1.1
unnamed: U40.3, U42.9
unnamed: U40.8, U42.12
unnamed: U40.11, U42.13
unnamed: U41.12 (~CE), U45.9 (~RCO)
unnamed: U42.3, U42.4
unnamed: U42.8, U44.9 (MR)
unnamed: U42.10, U42.11
unnamed: U43.3, U43.4
unnamed: U43.5, U43.8
PIXEL_CLOCK: U44.7 (CP)
PIXEL_DATA: R4.2, U44.13 (Q7)
RAM_A0: U46.2 (A0)
RAM_A1: U46.3 (A1)
RAM_A2: U46.4 (A2)
RAM_A3: U46.5 (A3)
RAM_A4: U46.6 (A4)
RAM_A5: U46.7 (A5)
RAM_A6: U46.8 (A6)
RAM_A7: U46.9 (A7)
RAM_A8: U12.2 (A0)
RAM_A9: U12.3 (A1)
RAM_A10: U12.4 (A2)
RAM_A11: U12.5 (A3)
RAM_A12: U12.6 (A4)
RAM_A13: U12.7 (A5)
RAM_A14: U12.8 (A6)
RAM_A15: U12.9 (A7)
V1: U43.9, U43.10, U45.7 (Q7), U46.12 (B6)
V2: U41.15 (Q0), U46.11 (B7)
V4: U12.18 (B0), U40.2, U41.1 (Q1), U43.12
V8: U12.17 (B1), U40.1, U41.2 (Q2)
V16: U12.16 (B2), U40.13, U41.3 (Q3)
V32: U12.15 (B3), U40.12, U41.4 (Q4)
V64: U12.14 (B4), U40.10, U41.5 (Q5)
V128: U12.13 (B5), U40.9, U41.6 (Q6)
V256: U41.7 (Q7), U43.13
~HSYNC: R3.2, U42.6
~PIXEL_LOAD: C6.2, U44.15 (PE)
~RESTART: U41.10 (~MRC), U43.2, U43.11, U45.10 (~MRC)
~VGA_ADDR_ON: U12.19 (CE), U46.19 (CE)
~VSYNC: R1.2, U43.1, U43.6

Notes on the sheet:
0xff00-0xffff is blanked. Only lines 0-251 are drawn.
The upper two bits select the VRAM bank at 0xc000.
Within a byte of VRAM the least significant bit appears on the screen at the *left hand side*.
~{S}
~{Q}
Capacitor forms an additional 10ns delay.
~{R}
