slu4coder/The-Minimal-64-Home-Computer/Revision 1.2/KiCAD/clock.kicad_sch

## KiCad design Revision 1.2/KiCAD/clock.kicad_sch (2023-07-08)

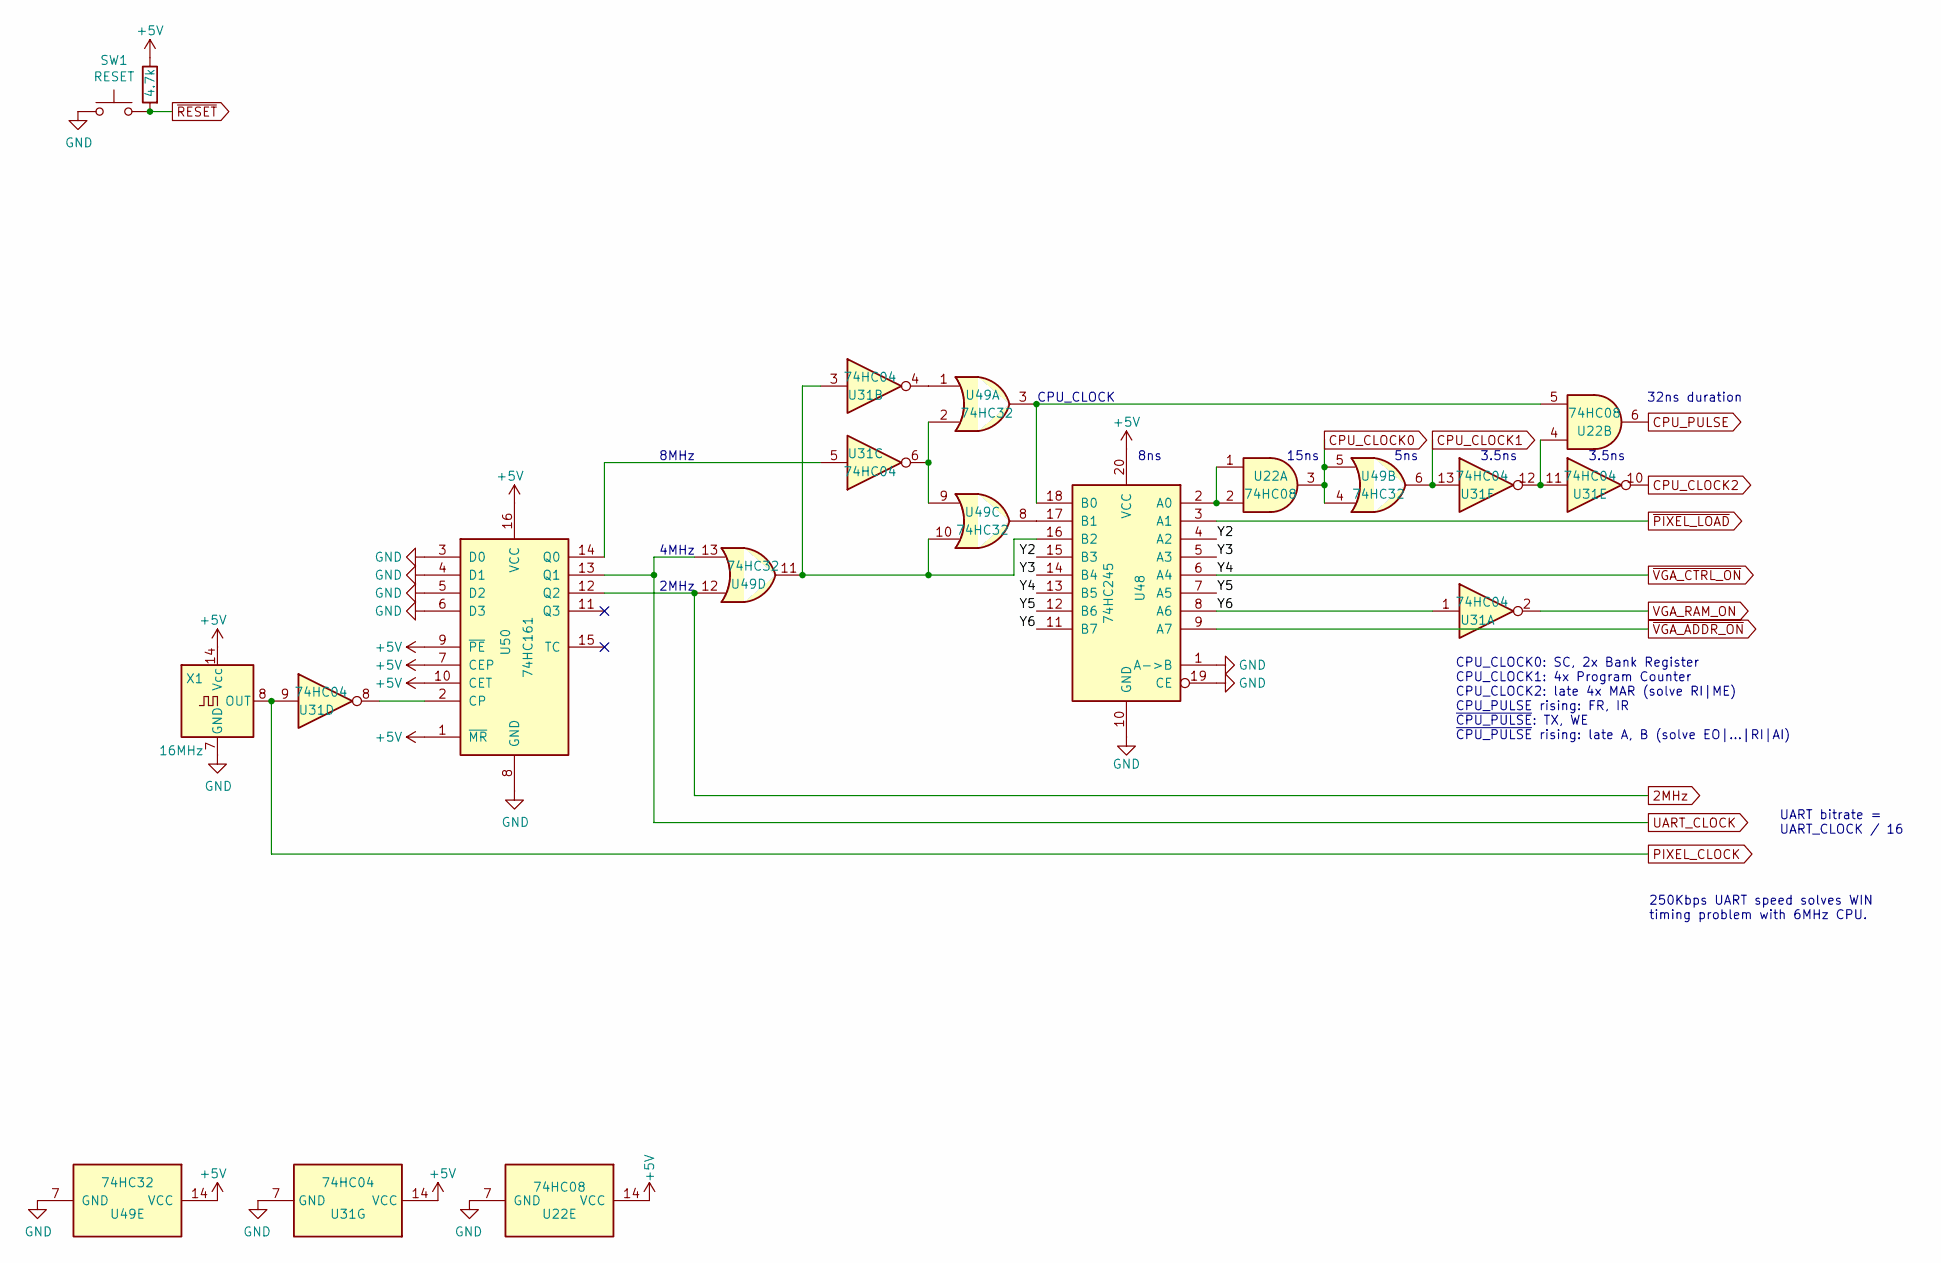
[picture p21: schematic clock.kicad_sch]

Parts:
R21: 4.7k; R_Axial_DIN0207_L6.3mm_D2.5mm_P7.62mm_Horizontal
SW1: RESET; SW_PUSH_6mm
U22: 74HC08; DIP-14_W7.62mm
U31: 74HC04; DIP-14_W7.62mm
U48: 74HC245; DIP-20_W7.62mm
U49: 74HC32; DIP-14_W7.62mm
U50: 74HC161; DIP-16_W7.62mm
X1: 16MHz; Oscillator_DIP-14

Connections:
2MHz: U49.12, U50.12 (Q2)
+5V: R21.1, U22.14 (VCC), U31.14 (VCC), U48.20 (VCC), U49.14 (VCC), U50.1 (~MR), U50.7 (CEP), U50.9 (~PE), U50.10 (CET), U50.16 (VCC), X1.14 (Vcc)
CPU_CLOCK0: U22.3, U49.4, U49.5
CPU_CLOCK1: U31.13, U49.6
CPU_CLOCK2: U31.10
CPU_PULSE: U22.6
GND: SW1.2, U22.7 (GND), U31.7 (GND), U48.1 (A->B), U48.10 (GND), U48.19 (CE), U49.7 (GND), U50.3 (D0), U50.4 (D1), U50.5 (D2), U50.6 (D3), U50.8 (GND), X1.7 (GND)
unnamed: U22.1, U22.2, U48.2 (A0)
unnamed: U22.4, U31.11, U31.12
unnamed: U22.5, U48.18 (B0), U49.3
unnamed: U31.3, U48.16 (B2), U49.10, U49.11
unnamed: U31.4, U49.1
unnamed: U31.5, U50.14 (Q0)
unnamed: U31.6, U49.2, U49.9
unnamed: U31.8, U50.2 (CP)
unnamed: U48.17 (B1), U49.8
PIXEL_CLOCK: U31.9, X1.8 (OUT)
UART_CLOCK: U49.13, U50.13 (Q1)
VGA_RAM_ON: U31.2
Y2: U48.4 (A2), U48.15 (B3)
Y3: U48.5 (A3), U48.14 (B4)
Y5: U48.7 (A5), U48.12 (B6)
Y6: U31.1, U48.8 (A6), U48.11 (B7)
~PIXEL_LOAD: U48.3 (A1)
~RESET: R21.2, SW1.1
~VGA_ADDR_ON: U48.9 (A7)
~VGA_CTRL_ON: U48.6 (A4), U48.13 (B5)

Notes on the sheet:
CPU_CLOCK0: SC, 2x Bank Register CPU_CLOCK1: 4x Program Counter CPU_CLOCK2: late 4x MAR (solve RI|ME) CPU_PULSE rising: FR, IR ~{CPU_PULSE}: TX, WE ~{CPU_PULSE} rising: late A, B (solve EO|...|RI|AI)
CPU_CLOCK
4MHz
5ns
8MHz
8ns
3.5ns
15ns
UART bitrate = UART_CLOCK / 16
32ns duration
2MHz
250Kbps UART speed solves WIN timing problem with 6MHz CPU.
