slu4coder/The-Minimal-64-Home-Computer/Revision 1.2/KiCAD/ps2.kicad_sch

## KiCad design Revision 1.2/KiCAD/ps2.kicad_sch (2023-07-08)

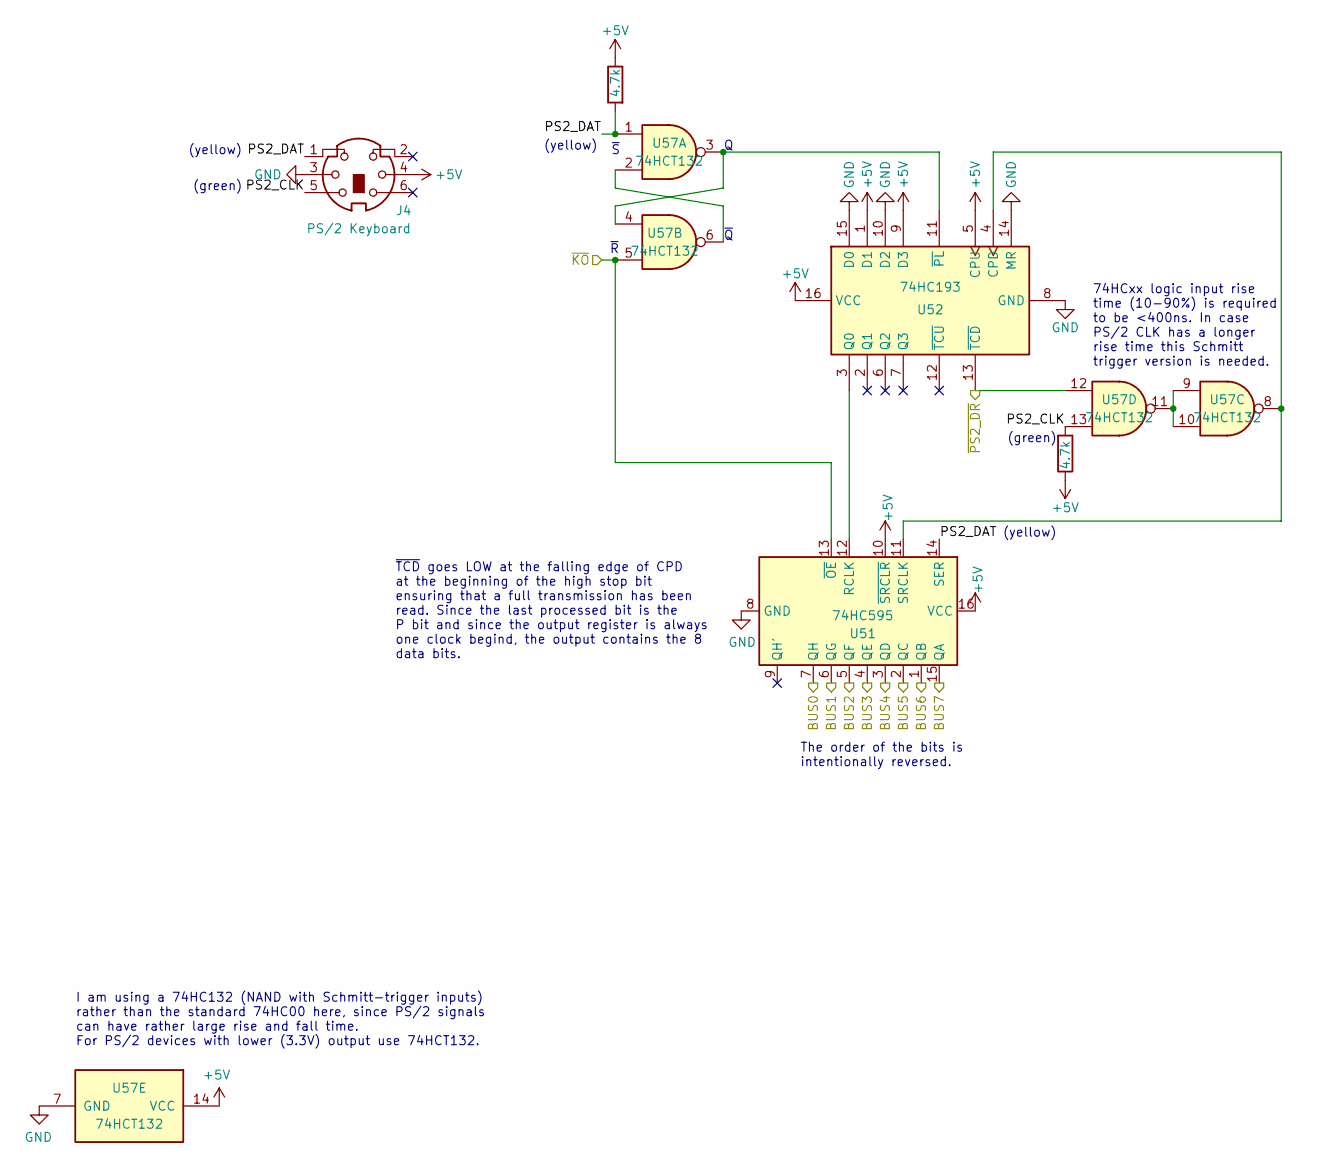
[picture p22: schematic ps2.kicad_sch]

Parts:
J4: PS/2 Keyboard; FP_MINI_DIN_6_PS2
R23, R24: 4.7k; R_Axial_DIN0207_L6.3mm_D2.5mm_P7.62mm_Horizontal
U51: 74HC595; DIP-16_W7.62mm
U52: 74HC193; DIP-16_W7.62mm
U57: 74HCT132; DIP-14_W7.62mm

Connections:
+5V: J4.4, R23.1, R24.1, U51.10 (~SRCLR), U51.16 (VCC), U52.1 (D1), U52.5 (CPU), U52.9 (D3), U52.16 (VCC), U57.14 (VCC)
BUS0: U51.7 (QH)
BUS1: U51.6 (QG)
BUS2: U51.5 (QF)
BUS3: U51.4 (QE)
BUS4: U51.3 (QD)
BUS5: U51.2 (QC)
BUS6: U51.1 (QB)
BUS7: U51.15 (QA)
GND: J4.3, U51.8 (GND), U52.8 (GND), U52.10 (D2), U52.14 (MR), U52.15 (D0), U57.7 (GND)
unnamed: U51.11 (SRCLK), U52.4 (CPD), U57.8
unnamed: U51.12 (RCLK), U52.3 (Q0)
unnamed: U52.11 (~PL), U57.3, U57.4
unnamed: U57.2, U57.6
unnamed: U57.9, U57.10, U57.11
PS2_CLK: J4.5, R24.2, U57.13
PS2_DAT: J4.1, R23.2, U51.14 (SER), U57.1
~KO: U51.13 (~OE), U57.5
~PS2_DR: U52.13 (~TCD), U57.12

Notes on the sheet:
(green)
(yellow)
~{Q}
The order of the bits is intentionally reversed.
~{TCD} goes LOW at the falling edge of CPD at the beginning of the high stop bit ensuring that a full transmission has been read. Since the last processed bit is the P bit and since the output register is always one clock begind, the output contains the 8 data bits.
~{R}
~{S}
74HCxx logic input rise time (10-90%) is required to be <400ns. In case PS/2 CLK has a longer rise time this Schmitt trigger version is needed.
I am using a 74HC132 (NAND with Schmitt-trigger inputs) rather than the standard 74HC00 here, since PS/2 signals can have rather large rise and fall time. For PS/2 devices with lower (3.3V) output use 74HCT132.
