slu4coder/The-Minimal-64-Home-Computer/Programs/asm/birds.asm

#org 0x8000       LDI 0x0c STA dst+0 LDI 0xc3 STA dst+1
                  LDI <pic STA src+0 LDI >pic STA src+1
                  LYI 240
yloop:            LXI 50
xloop:            LDA
src:              0xffff STA
dst:              0xffff INW src INW dst DEX BGT xloop
                    LDI 14 ADW dst
                    DEY BGT yloop
                      JPS 0xb02a    ; _WaitInput
                      JPA 0xb003    ; _Prompt
pic:
0x00,0x00,0x00,0x08,0x1b,0x00,0x00,0x00,0x00,0x00,0x00,0x00,0x00,0x00,0xc0,0xfd,0xff,0xff,0xff,0x7f,0x22,0x00,0x00,0x00,0x00,0x30,0x19,0x00,0x00,0x00,0x00,0x00,0x00,0x40,0x95,0x24,0x01,0x00,0x00,0x00,0x00,0x00,0x00,0x00,0x00,0x00,0x00,0x00,0x00,0x00,
0x00,0x40,0x24,0x82,0x33,0x49,0x15,0x00,0x00,0x00,0x00,0x00,0x00,0x80,0x60,0x93,0x2f,0xff,0x7f,0x2b,0x11,0x24,0x01,0x00,0x00,0x98,0x28,0x00,0x00,0x00,0x00,0x00,0x02,0xc0,0x76,0x2b,0x4a,0x02,0x00,0x00,0x00,0x00,0x00,0x00,0x00,0x00,0x40,0x12,0x01,0x00,
0x00,0x80,0x10,0x94,0x29,0x22,0x48,0x14,0x00,0x00,0x00,0x00,0x00,0x00,0xa0,0xee,0xba,0xed,0xed,0x97,0x44,0x24,0x12,0x00,0x00,0x84,0x18,0x00,0x00,0x00,0x00,0x90,0x00,0x80,0xab,0x54,0x11,0xa4,0x24,0x09,0x00,0x00,0x00,0x00,0x50,0x2b,0x09,0x80,0x48,0x92,
0x00,0x10,0x11,0xb0,0x15,0x00,0x00,0x40,0x00,0x00,0x00,0x00,0x00,0x80,0x20,0x7d,0xd7,0x7d,0xdf,0x92,0x28,0x44,0x48,0x02,0x00,0xc4,0x0c,0x00,0x00,0x00,0x00,0x02,0x01,0x80,0xcd,0x22,0xa1,0x10,0x80,0xa0,0x04,0x40,0x10,0x49,0x05,0x00,0x00,0x01,0x00,0x00,
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
0x00,0x93,0x20,0x7a,0x40,0x09,0x7e,0xc0,0x48,0xa9,0xeb,0x7e,0x00,0x00,0x00,0x00,0x80,0x10,0xf2,0xad,0xda,0x2b,0x3a,0x44,0x04,0x00,0x6f,0x05,0x80,0x69,0x65,0x2a,0xa4,0x80,0x0d,0x00,0x00,0xfe,0xff,0xff,0x00,0x04,0x09,0x00,0x00,0x02,0x00,0x00,0x02,0x00,
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
